gowenrw/cowboys_vs_dinosaurs/art/Card2-jack.png

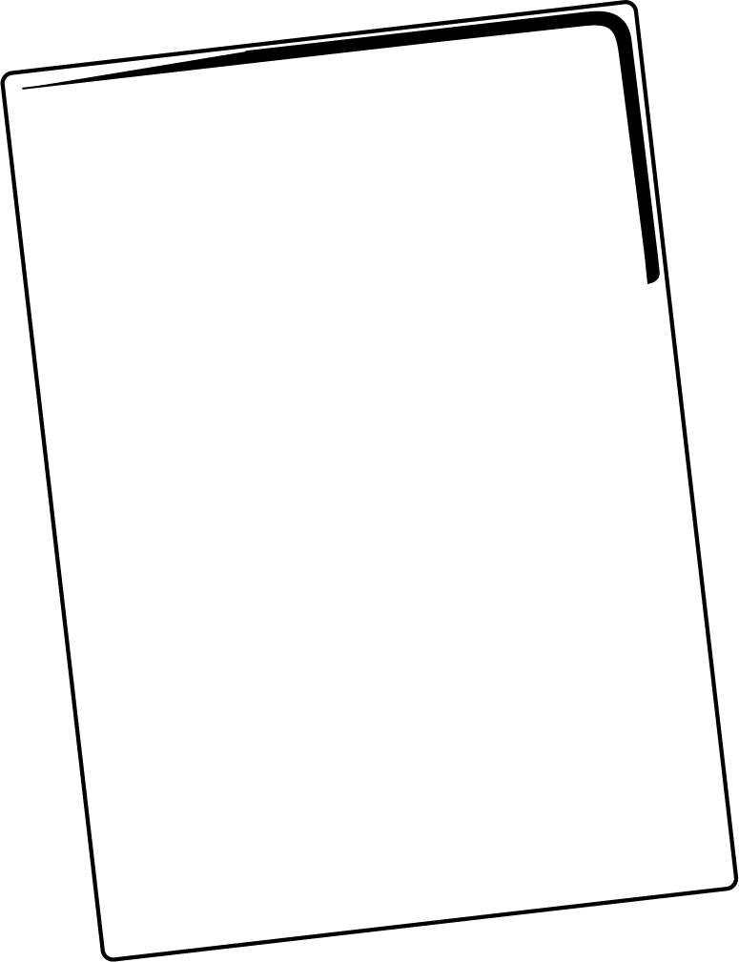
art/Card2-jack.png
