gowenrw/cowboys_vs_dinosaurs/art/Card2-king-01.png

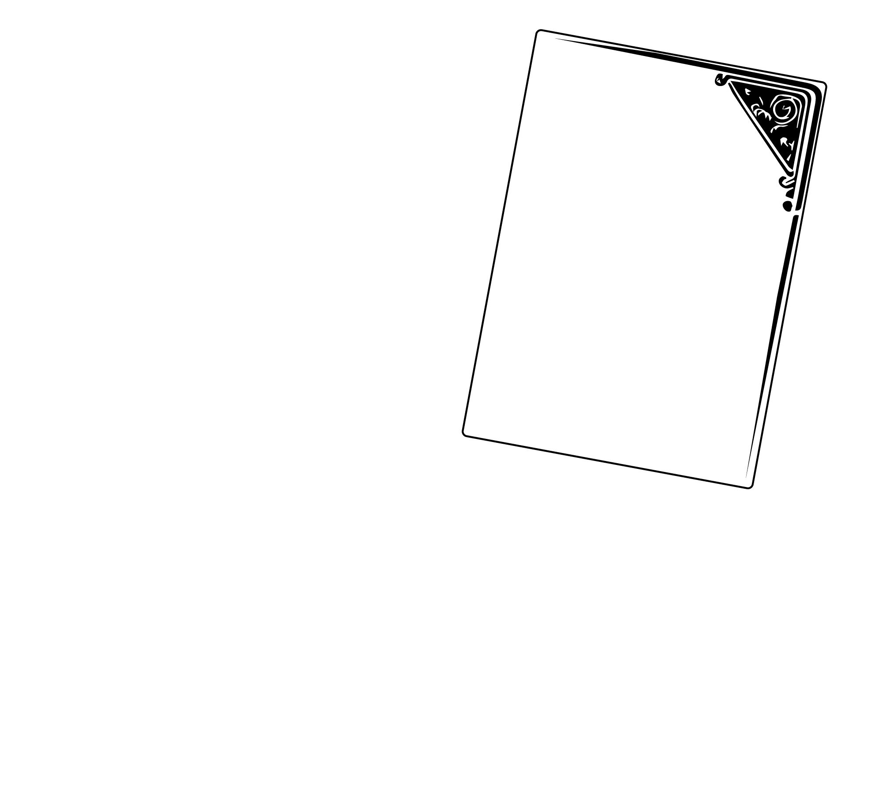
art/Card2-king-01.png
