gowenrw/cowboys_vs_dinosaurs/art/Card2-queen.png

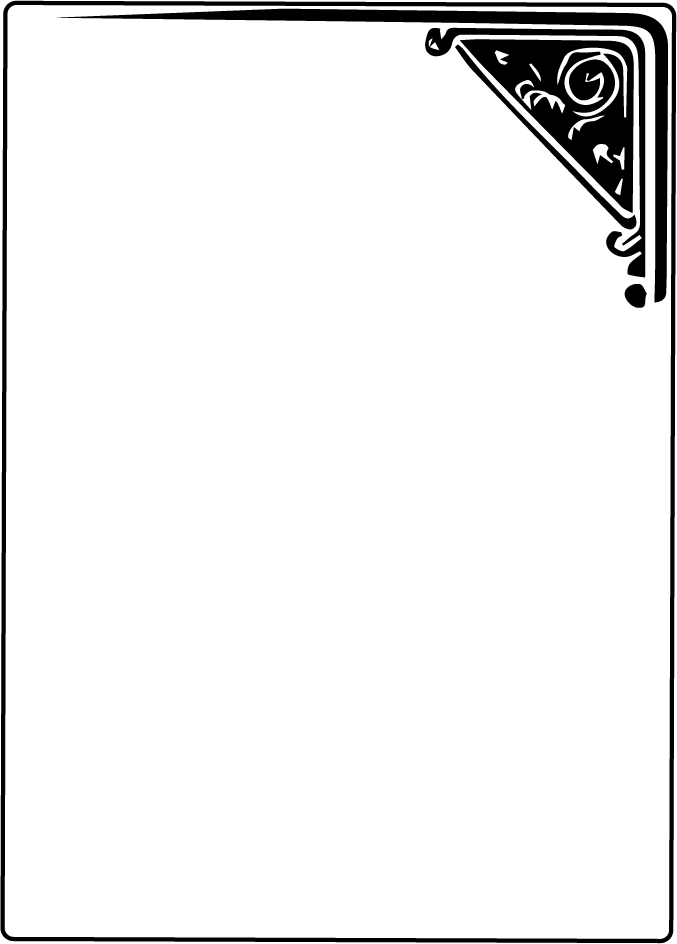
art/Card2-queen.png
