gowenrw/cowboys_vs_dinosaurs/art/Card2-suits-01.png

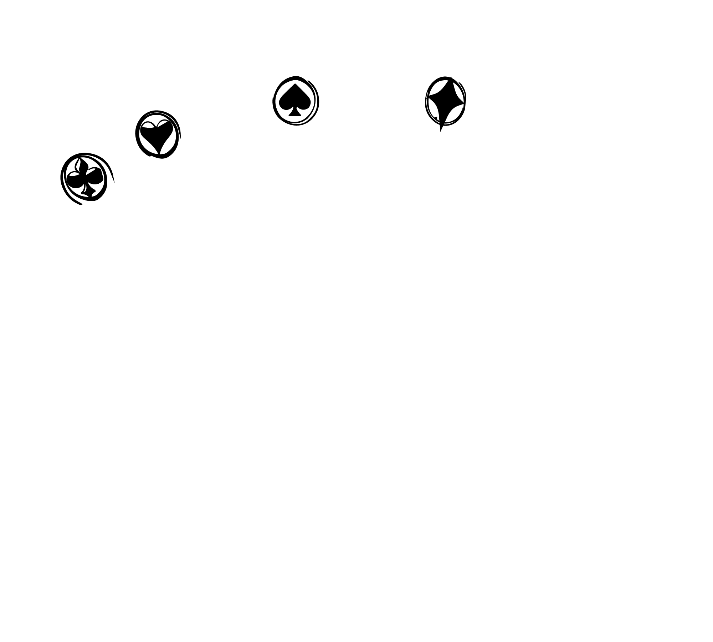
art/Card2-suits-01.png
