gowenrw/cowboys_vs_dinosaurs/art/Card2-ten.png

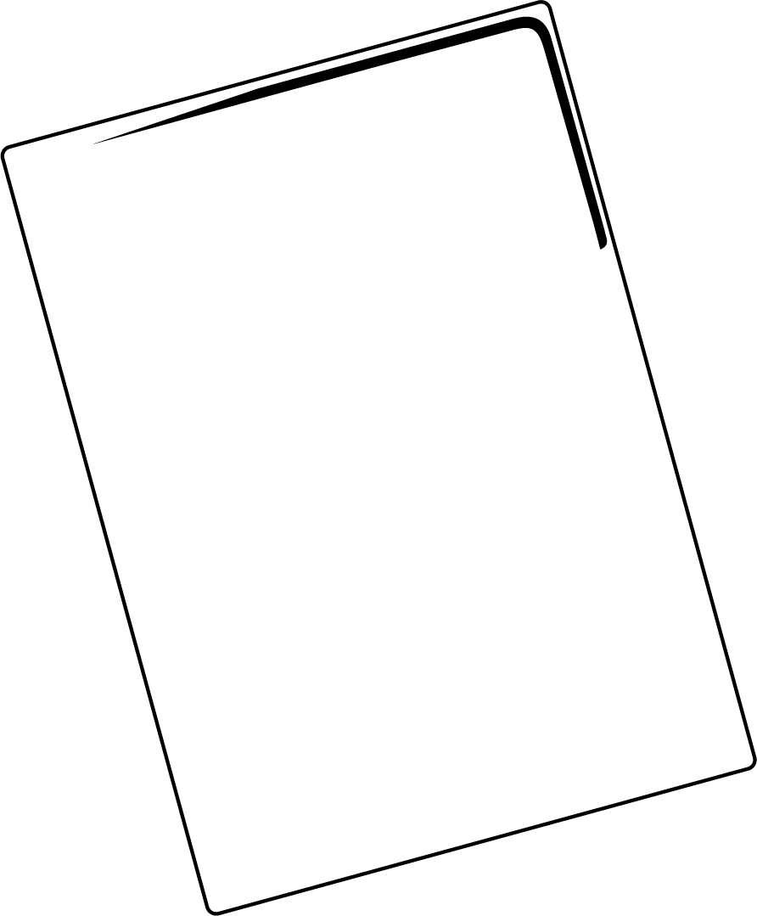
art/Card2-ten.png
