gowenrw/cowboys_vs_dinosaurs/art/card.png

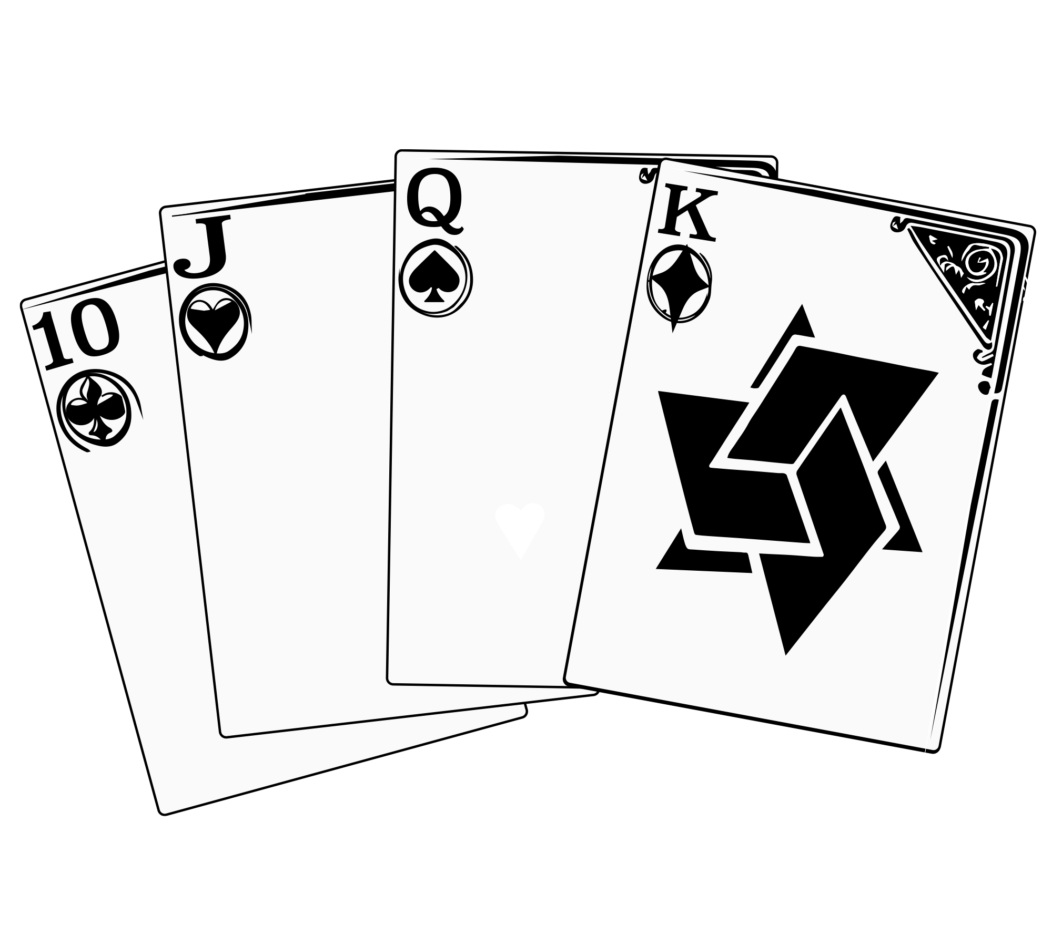
art/card.png
