gowenrw/cowboys_vs_dinosaurs/art/customlanyard_proof.png

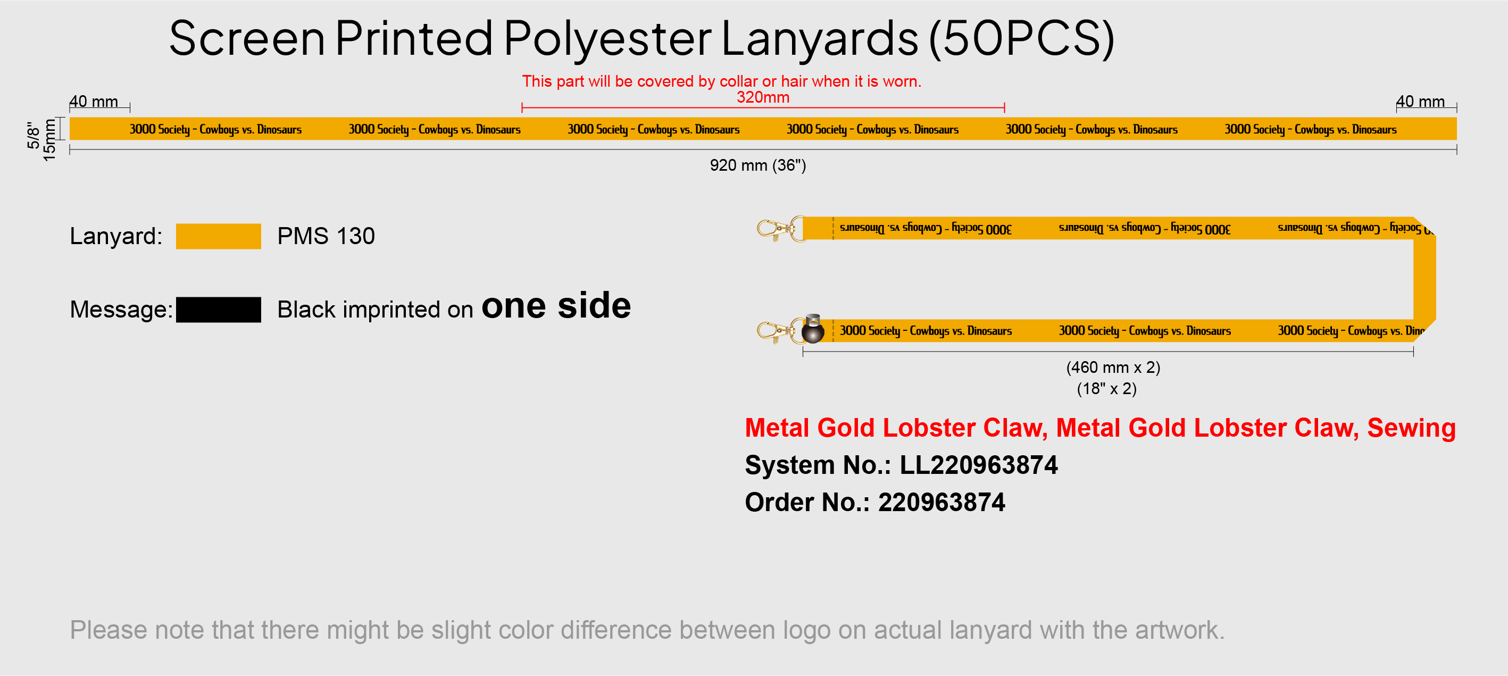
art/customlanyard_proof.png
