gowenrw/cowboys_vs_dinosaurs/art/CvD_Concept_Layout_2_Edge-01.jpg

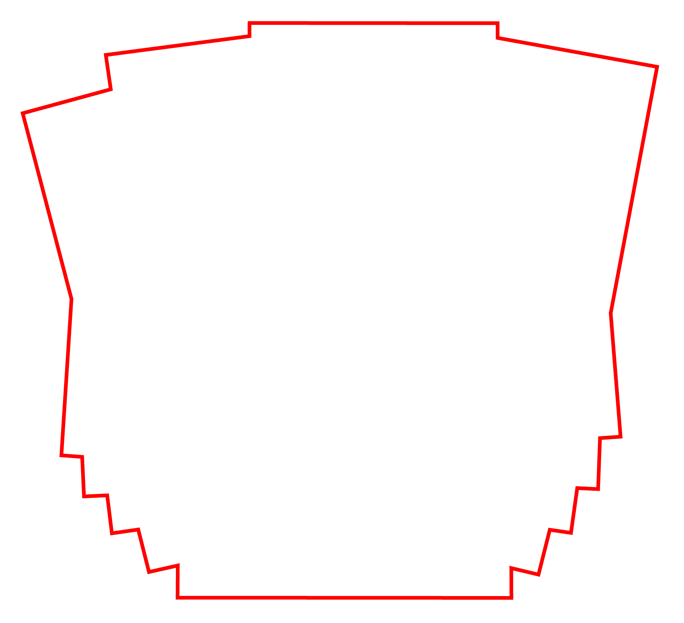
art/CvD_Concept_Layout_2_Edge-01.jpg
