gowenrw/cowboys_vs_dinosaurs/art/cvd_sticker.jpg

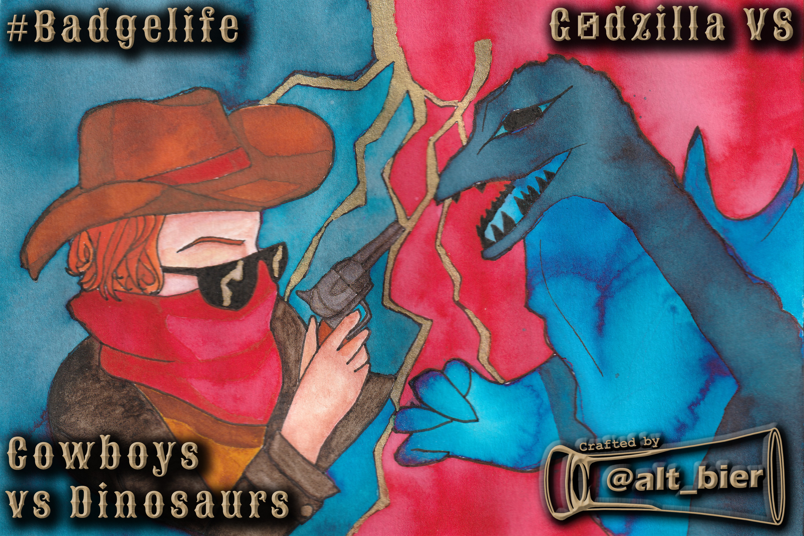
art/cvd_sticker.jpg
