gowenrw/cowboys_vs_dinosaurs/art/Dinosaurs_playing_poker_with_Cowboys_Rev01-01.png

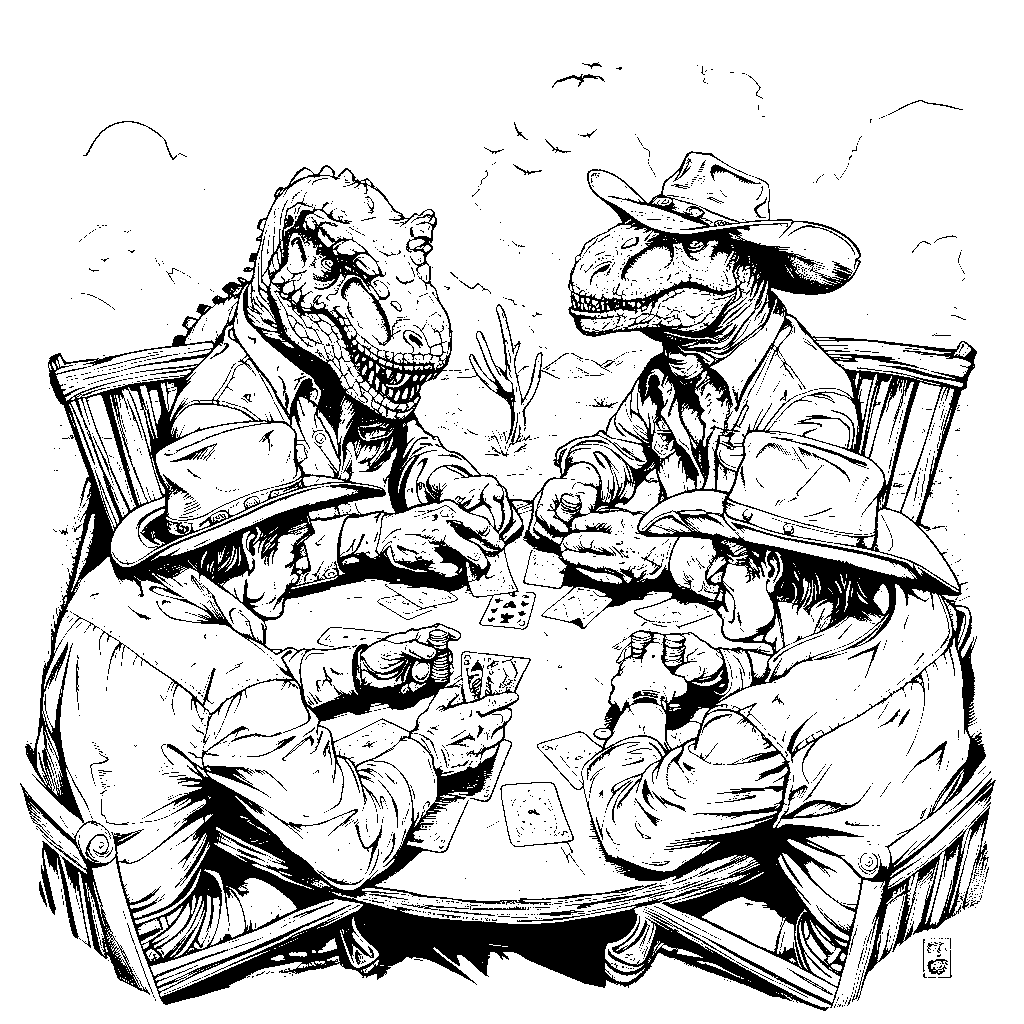
art/Dinosaurs_playing_poker_with_Cowboys_Rev01-01.png
