gowenrw/cowboys_vs_dinosaurs/art/Dinosaurs_playing_poker_with_Cowboys_Rev03_poker.png

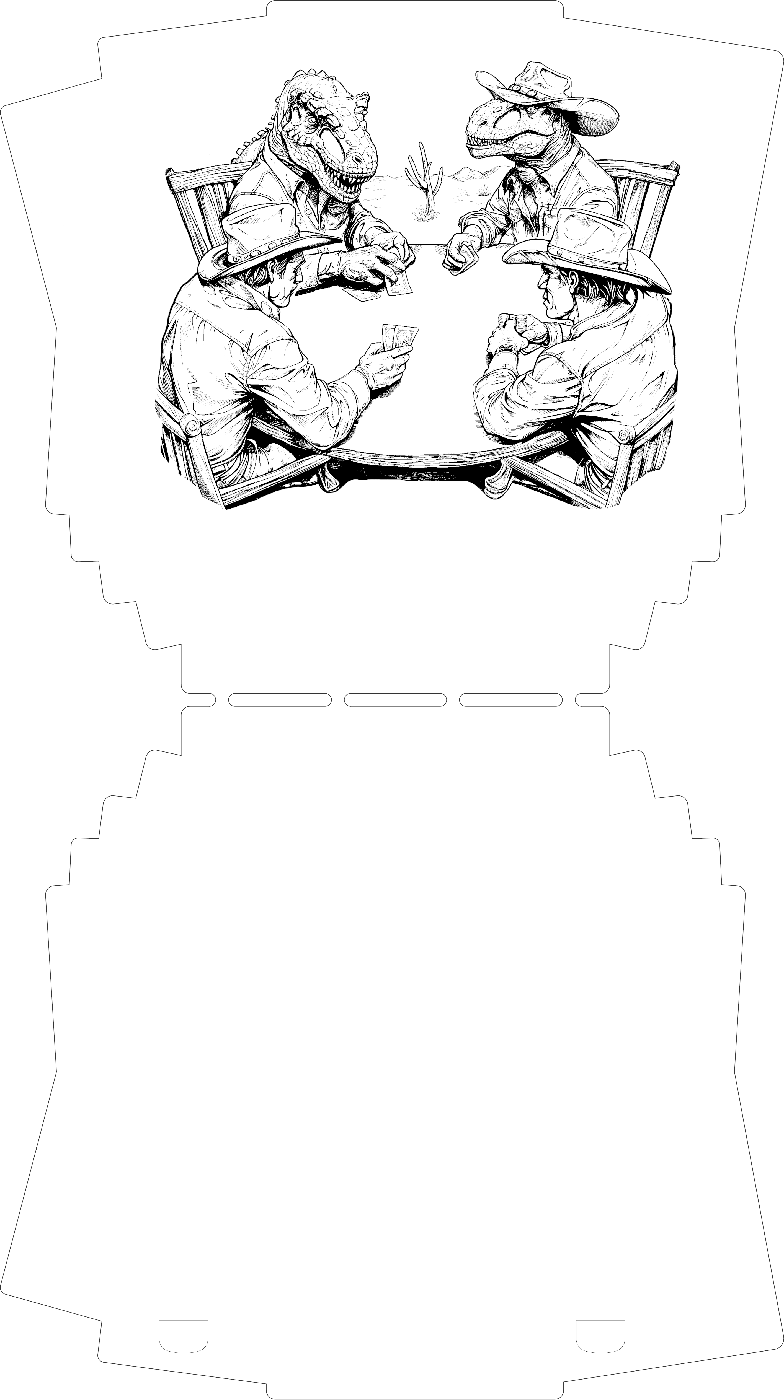
art/Dinosaurs_playing_poker_with_Cowboys_Rev03_poker.png
