gowenrw/cowboys_vs_dinosaurs/art/Dinosaurs_playing_poker_with_Cowboys_Rev03_tableback_mask.png

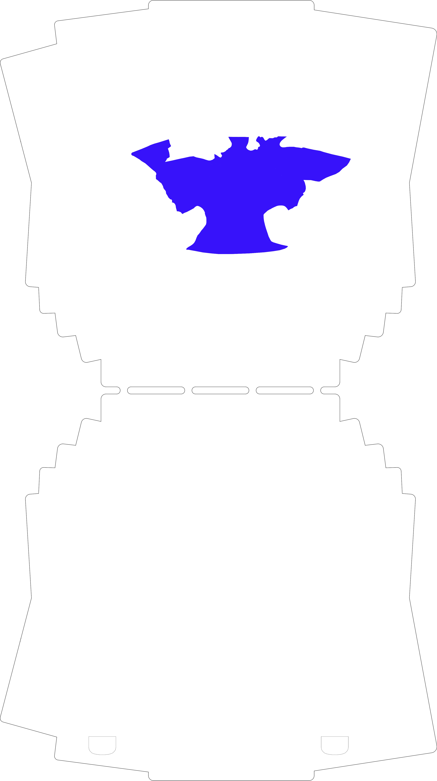
art/Dinosaurs_playing_poker_with_Cowboys_Rev03_tableback_mask.png
