gowenrw/cowboys_vs_dinosaurs/art/Dinosaurs_playing_poker_with_Cowboys_Rev04_cards_top.png

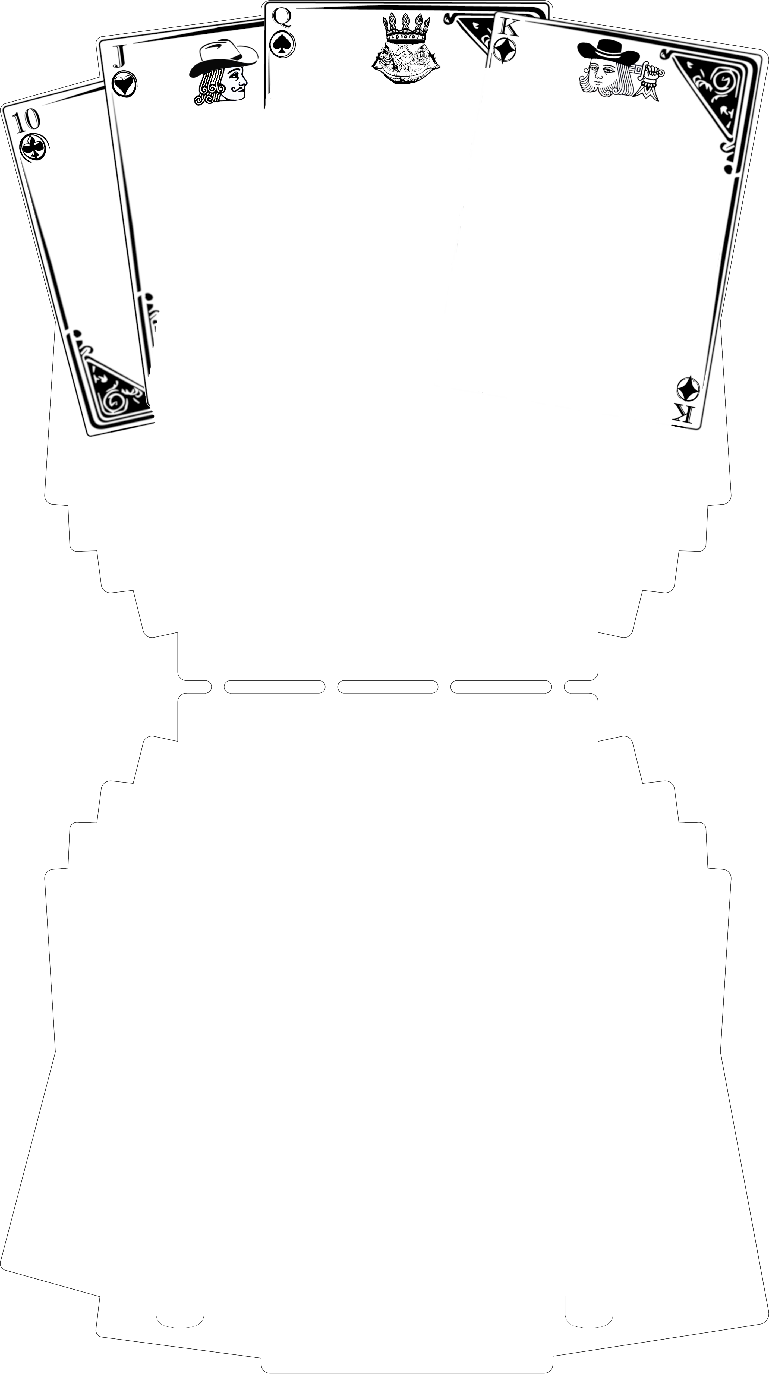
art/Dinosaurs_playing_poker_with_Cowboys_Rev04_cards_top.png
