gowenrw/cowboys_vs_dinosaurs/art/inspiration/alt_bier_cowbow_fighting_dinosaur_western_desert_f3125613-8451-445c-b527-2a0ff5816ff6.png

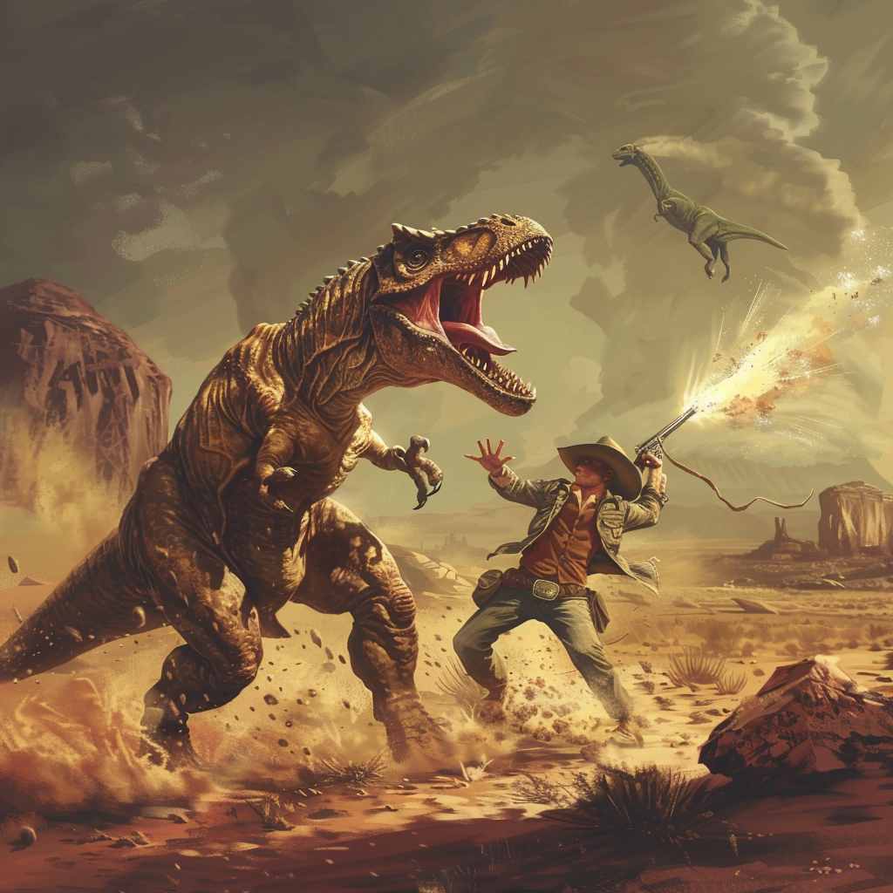
art/inspiration/alt_bier_cowbow_fighting_dinosaur_western_desert_f3125613-8451-445c-b527-2a0ff5816ff6.png
