gowenrw/cowboys_vs_dinosaurs/art/inspiration/alt_bier_cowbows_fighting_dinosaurs_on_western_plains_lineart_a25336c1-f8a5-47d8-abfa-79130a526ea2.png

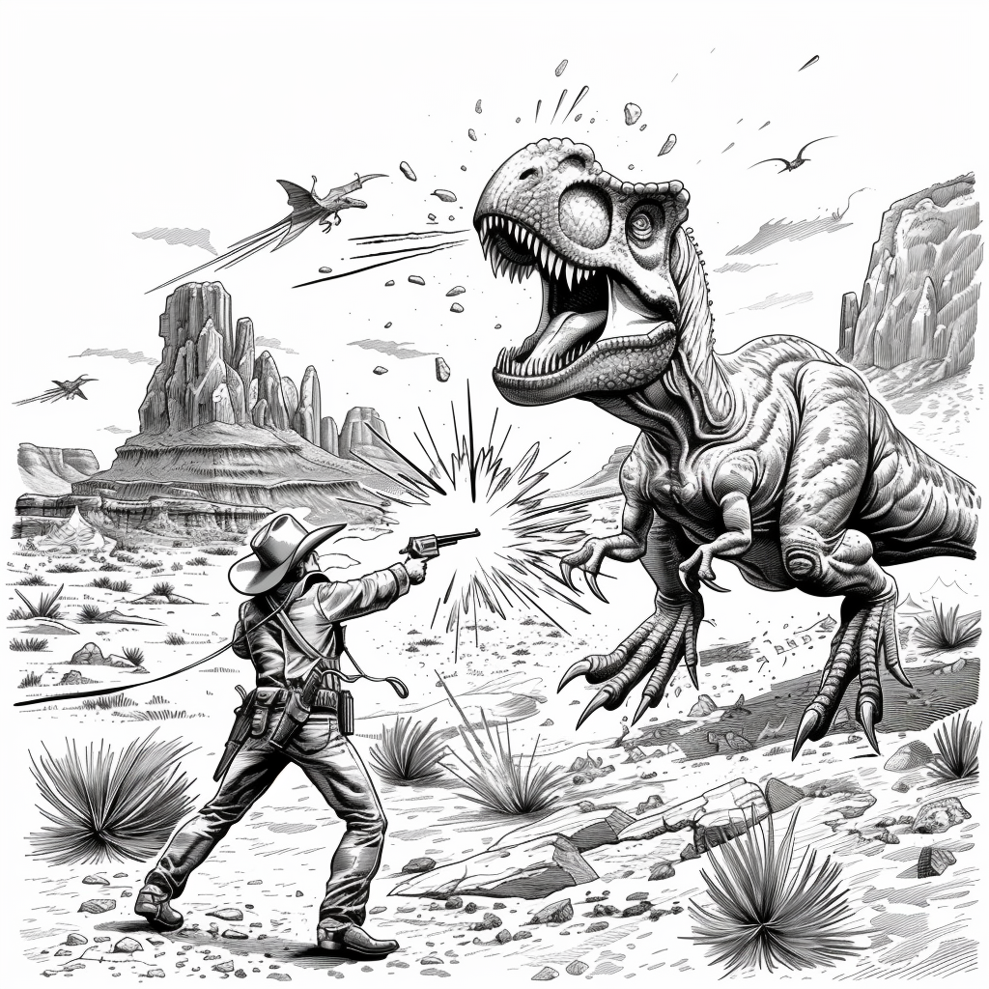
art/inspiration/alt_bier_cowbows_fighting_dinosaurs_on_western_plains_lineart_a25336c1-f8a5-47d8-abfa-79130a526ea2.png
