gowenrw/cowboys_vs_dinosaurs/art/inspiration/alt_bier_cowbows_fighting_dinosaurs_on_western_plains_lineart_f211f42e-96e7-4485-8ce5-57ef15629b50.png

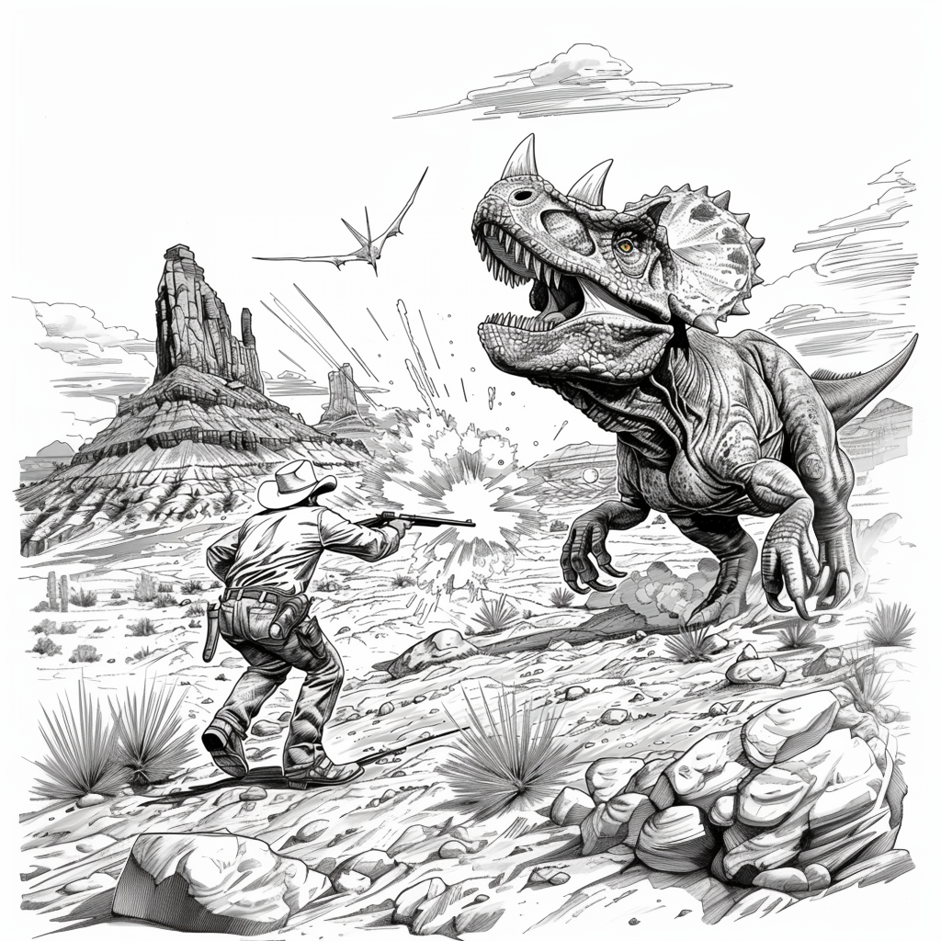
art/inspiration/alt_bier_cowbows_fighting_dinosaurs_on_western_plains_lineart_f211f42e-96e7-4485-8ce5-57ef15629b50.png
