gowenrw/cowboys_vs_dinosaurs/art/inspiration/alt_bier_Cowboy_fighting_dinosaur_western_desert_lineart_in_the_3fcf7f37-1b51-49f2-8be1-fd573b53e4d1.png

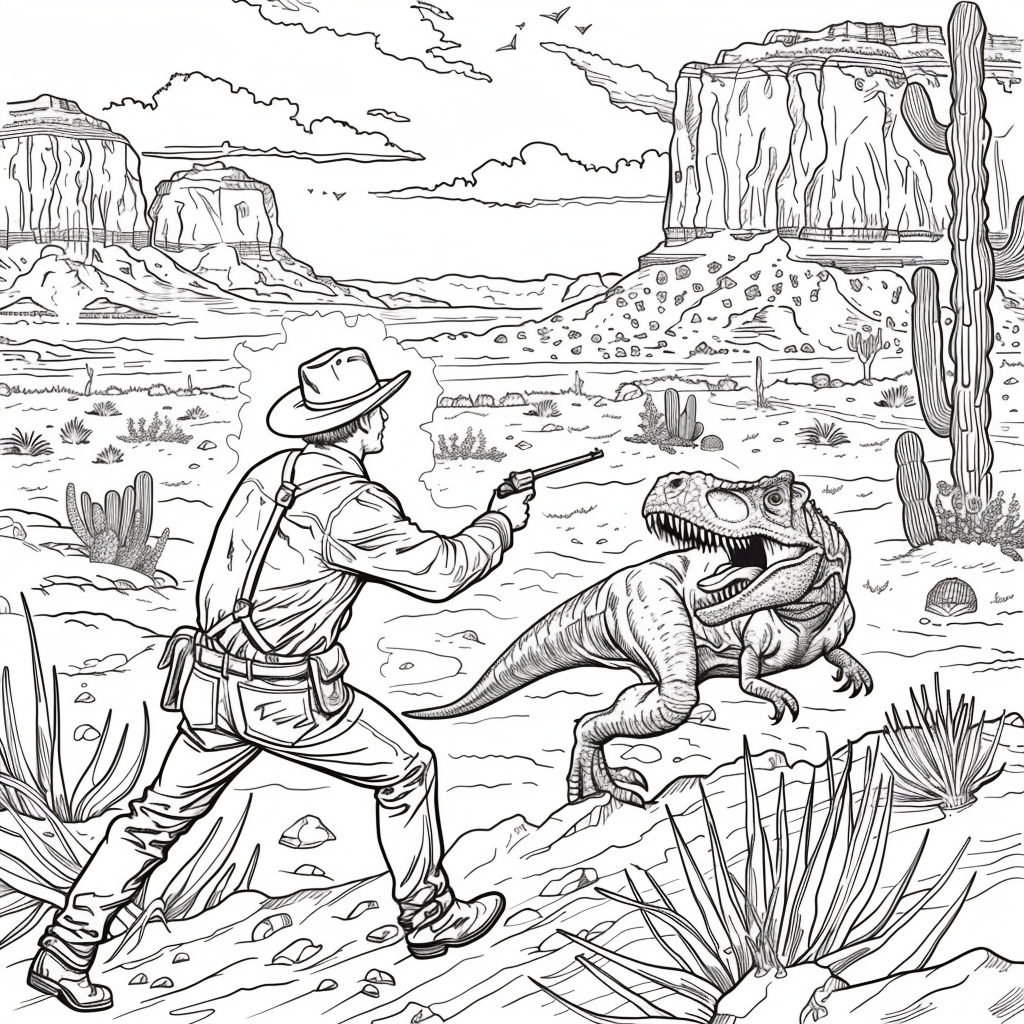
art/inspiration/alt_bier_Cowboy_fighting_dinosaur_western_desert_lineart_in_the_3fcf7f37-1b51-49f2-8be1-fd573b53e4d1.png
