gowenrw/cowboys_vs_dinosaurs/art/inspiration/alt_bier_Cowboy_fighting_dinosaur_western_desert_lineart_in_the_5abc0463-220d-4dce-b457-b19400f9878a.png

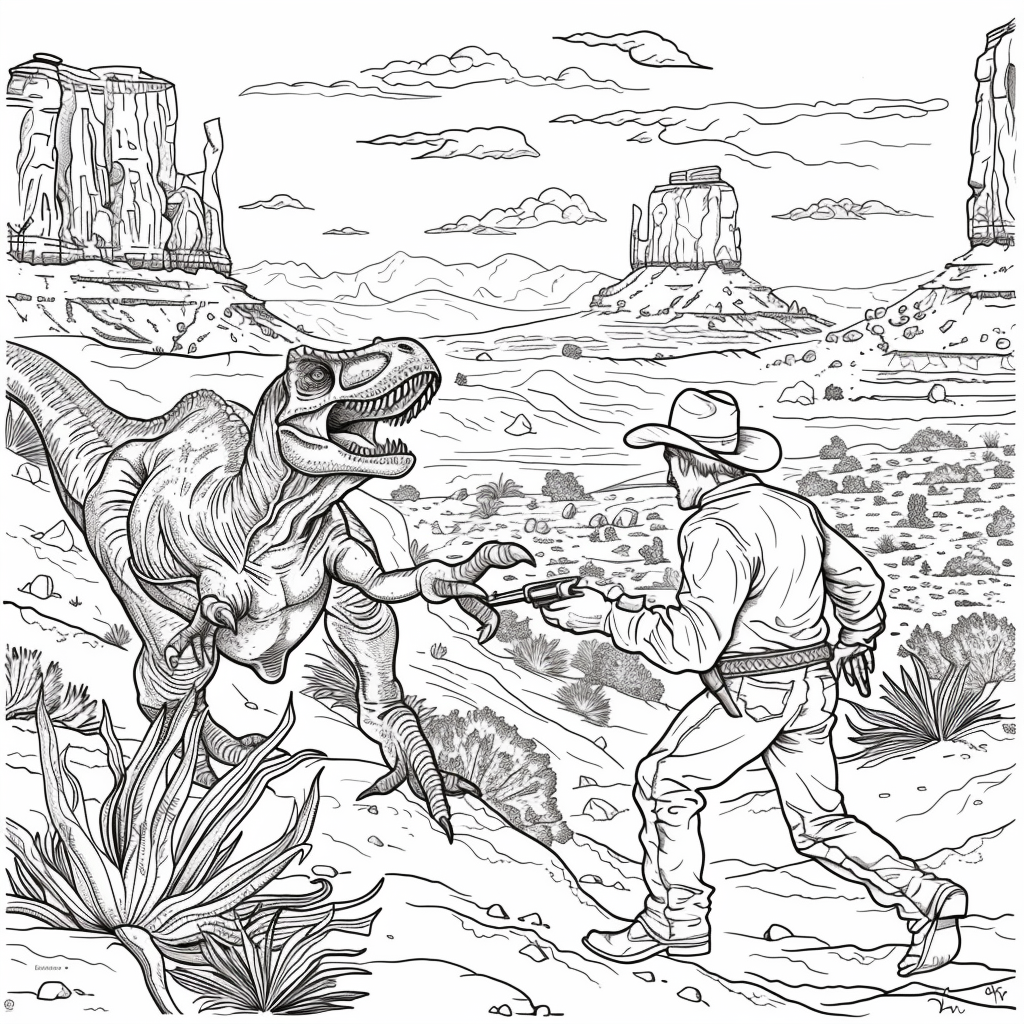
art/inspiration/alt_bier_Cowboy_fighting_dinosaur_western_desert_lineart_in_the_5abc0463-220d-4dce-b457-b19400f9878a.png
