gowenrw/cowboys_vs_dinosaurs/art/inspiration/alt_bier_Cowboy_fighting_dinosaur_western_desert_lineart_in_the_125ab11b-fa4d-480e-95ab-365c5027ad4b.png

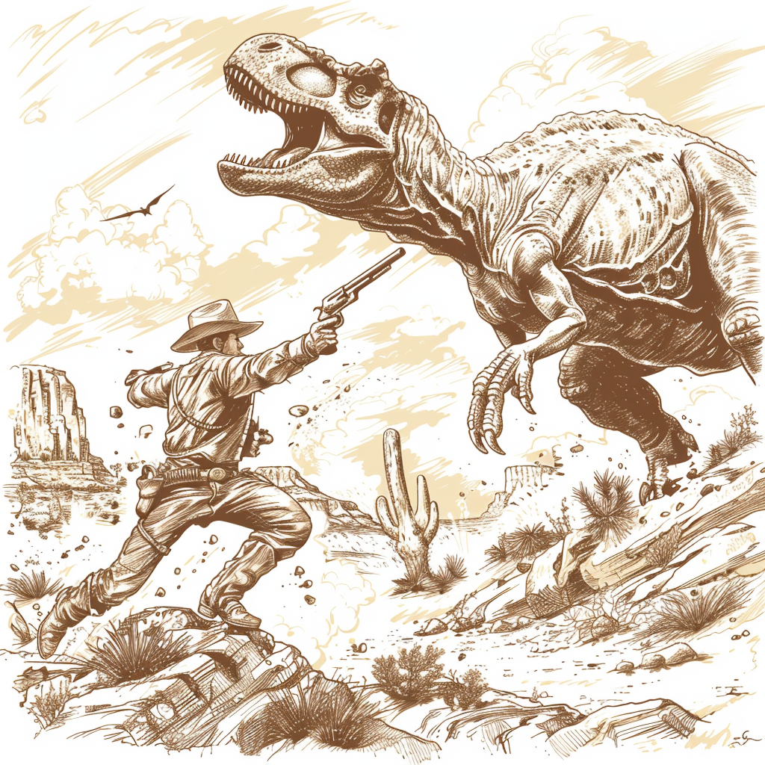
art/inspiration/alt_bier_Cowboy_fighting_dinosaur_western_desert_lineart_in_the_125ab11b-fa4d-480e-95ab-365c5027ad4b.png
