gowenrw/cowboys_vs_dinosaurs/art/inspiration/alt_bier_Cowboy_fighting_dinosaur_western_desert_lineart_in_the_282fbab5-89a2-4fbe-8cb0-ce9cdb12c011.png

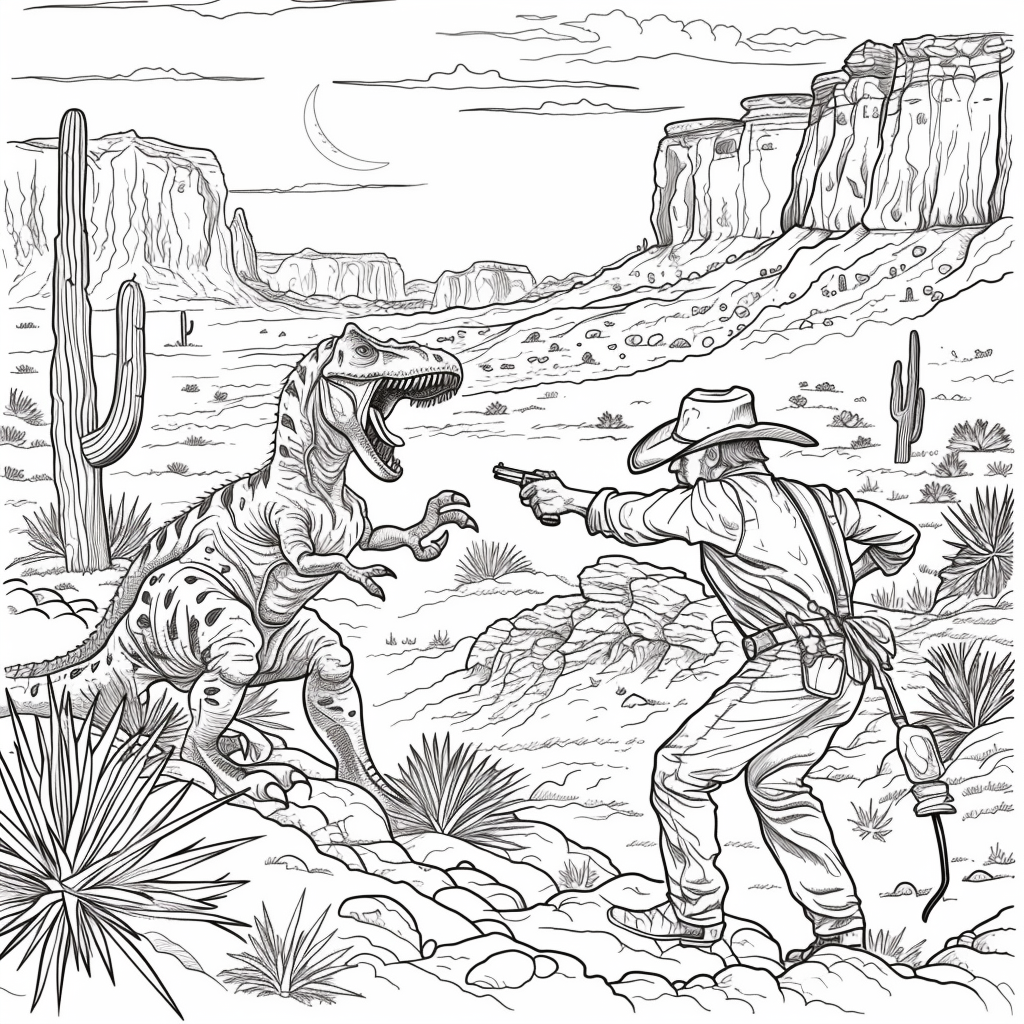
art/inspiration/alt_bier_Cowboy_fighting_dinosaur_western_desert_lineart_in_the_282fbab5-89a2-4fbe-8cb0-ce9cdb12c011.png
