gowenrw/cowboys_vs_dinosaurs/art/inspiration/alt_bier_Cowboy_fighting_dinosaur_western_desert_lineart_in_the_556321d8-3b47-4c62-af58-bf69dc58ff7b.png

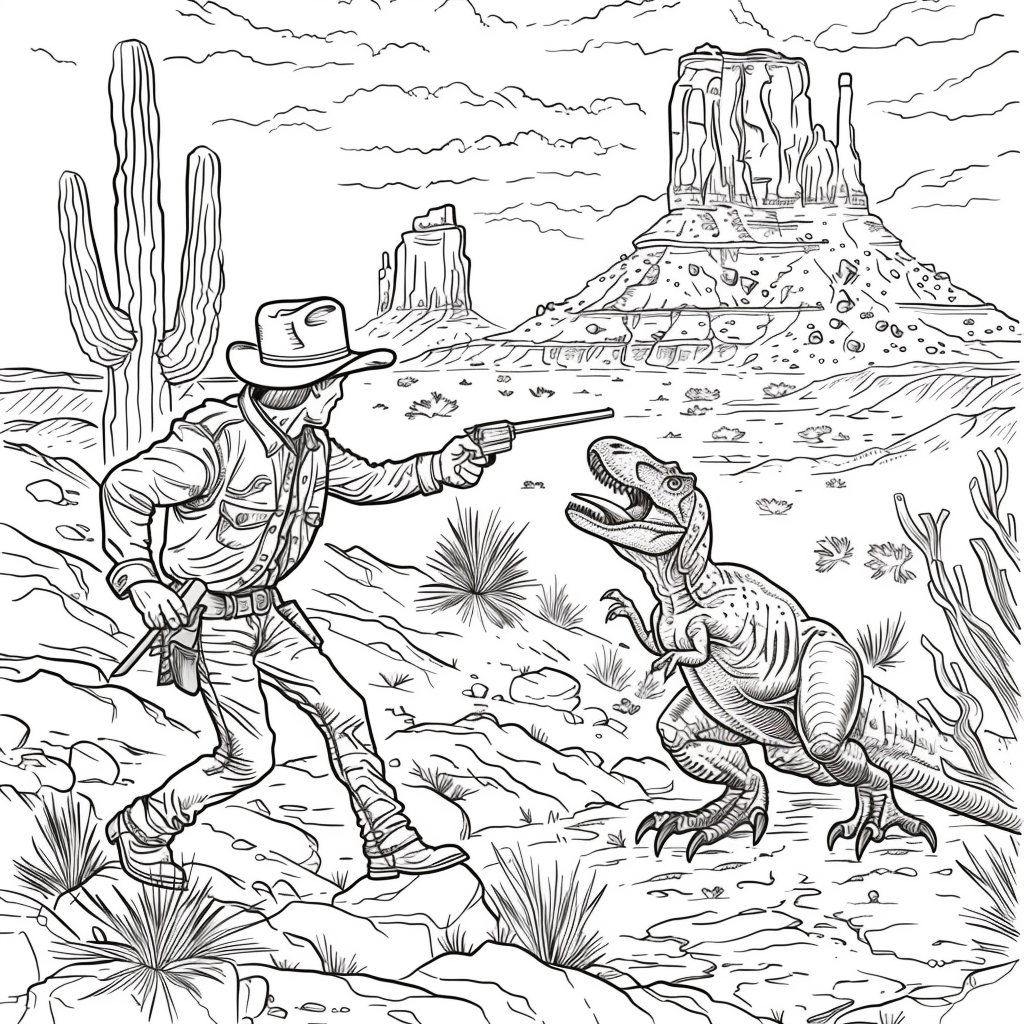
art/inspiration/alt_bier_Cowboy_fighting_dinosaur_western_desert_lineart_in_the_556321d8-3b47-4c62-af58-bf69dc58ff7b.png
