gowenrw/cowboys_vs_dinosaurs/art/inspiration/alt_bier_Cowboy_shooting_at_a_giant_Tyrannosaurus_western_deser_4aaeae45-6dd6-4bee-8e14-5fdc8e3b1cd2.png

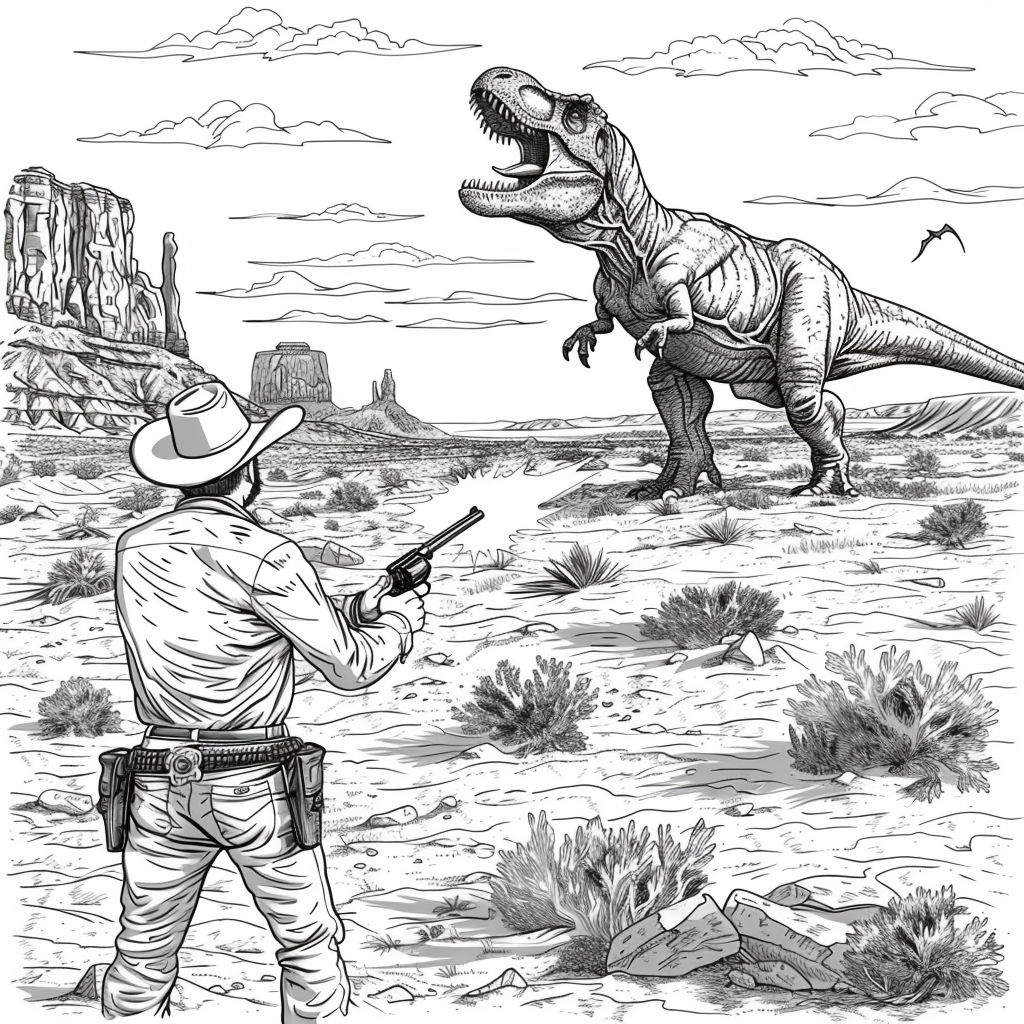
art/inspiration/alt_bier_Cowboy_shooting_at_a_giant_Tyrannosaurus_western_deser_4aaeae45-6dd6-4bee-8e14-5fdc8e3b1cd2.png
