gowenrw/cowboys_vs_dinosaurs/art/inspiration/alt_bier_Cowboy_shooting_at_a_giant_Tyrannosaurus_western_deser_bf7210f8-492b-4deb-bcf0-d93d4ab07705.png

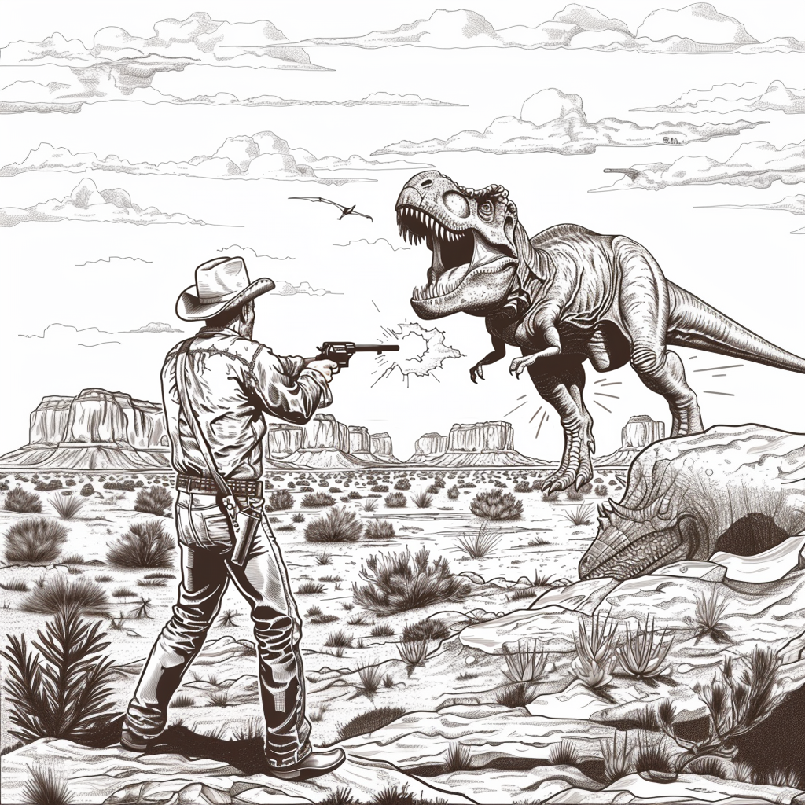
art/inspiration/alt_bier_Cowboy_shooting_at_a_giant_Tyrannosaurus_western_deser_bf7210f8-492b-4deb-bcf0-d93d4ab07705.png
