gowenrw/cowboys_vs_dinosaurs/art/inspiration/alt_bier_Dinosaurs_and_cowboys_playing_poker_coloring_book_no_c_4e8ae06e-67b5-412c-8ffb-398090f191ba.png

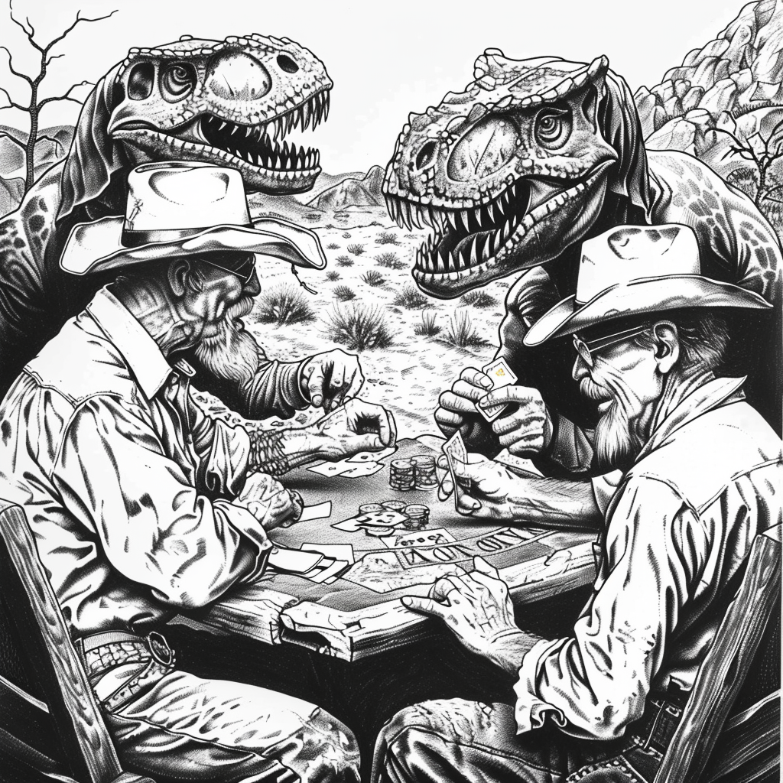
art/inspiration/alt_bier_Dinosaurs_and_cowboys_playing_poker_coloring_book_no_c_4e8ae06e-67b5-412c-8ffb-398090f191ba.png
