gowenrw/cowboys_vs_dinosaurs/art/inspiration/alt_bier_Dinosaurs_and_cowboys_playing_poker_in_the_style_of_do_59055e36-9cf2-4947-9dd1-eef9e1b4fb1d.png

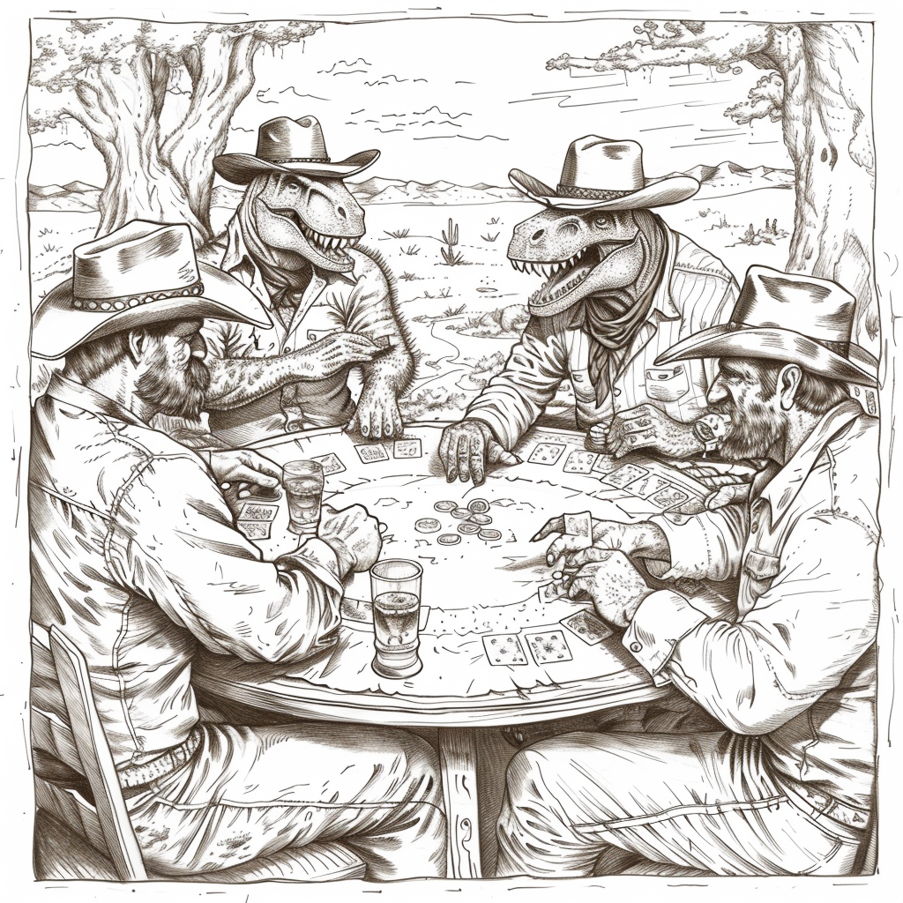
art/inspiration/alt_bier_Dinosaurs_and_cowboys_playing_poker_in_the_style_of_do_59055e36-9cf2-4947-9dd1-eef9e1b4fb1d.png
