gowenrw/cowboys_vs_dinosaurs/art/inspiration/alt_bier_Dinosaurs_playing_poker_with_cowboys_in_the_style_of_D_9a29f2ae-062c-44e6-b967-7e2f51b78c59.png

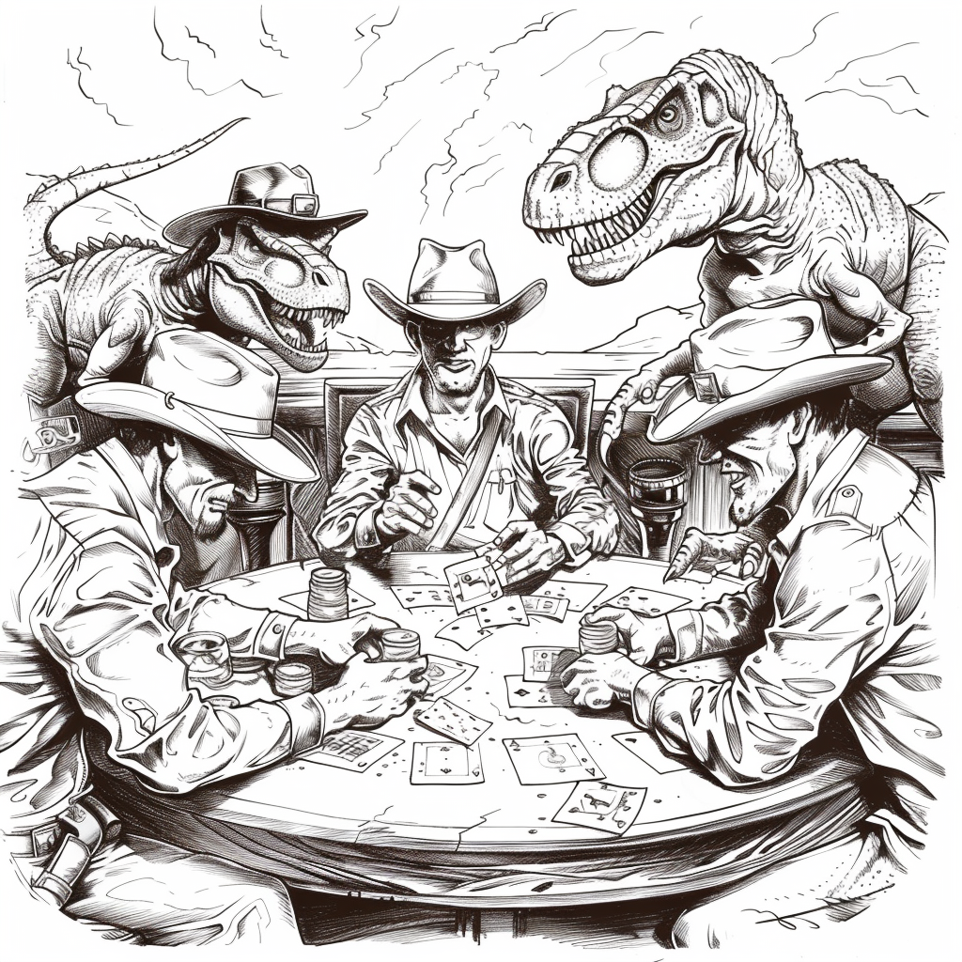
art/inspiration/alt_bier_Dinosaurs_playing_poker_with_cowboys_in_the_style_of_D_9a29f2ae-062c-44e6-b967-7e2f51b78c59.png
