gowenrw/cowboys_vs_dinosaurs/art/inspiration/alt_bier_Dinosaurs_playing_poker_with_cowboys_in_the_style_of_D_9ae7338b-8200-457a-bcaf-93dff62f932e.png

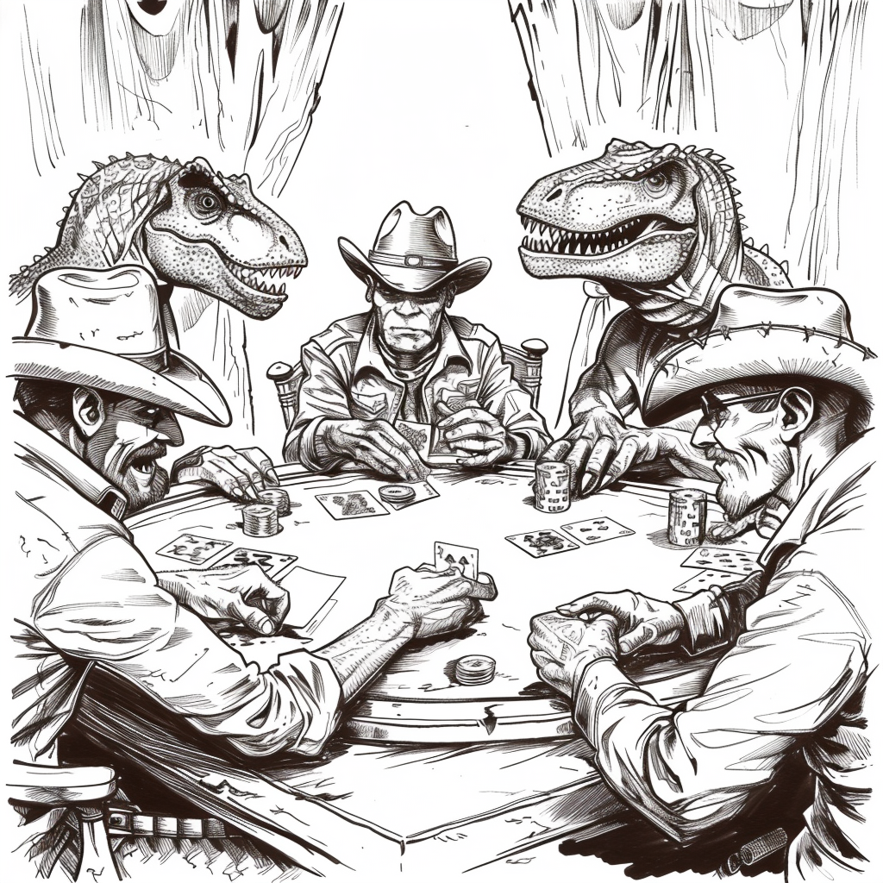
art/inspiration/alt_bier_Dinosaurs_playing_poker_with_cowboys_in_the_style_of_D_9ae7338b-8200-457a-bcaf-93dff62f932e.png
