gowenrw/cowboys_vs_dinosaurs/art/labels/cowboys_vs_dinos_ass.jpg

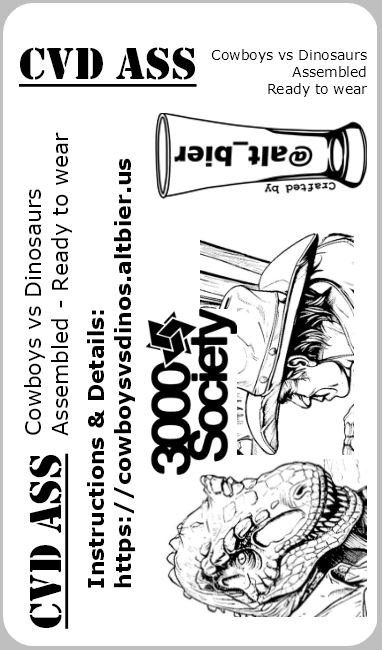
art/labels/cowboys_vs_dinos_ass.jpg
