gowenrw/cowboys_vs_dinosaurs/art/Lanyard_txt.png

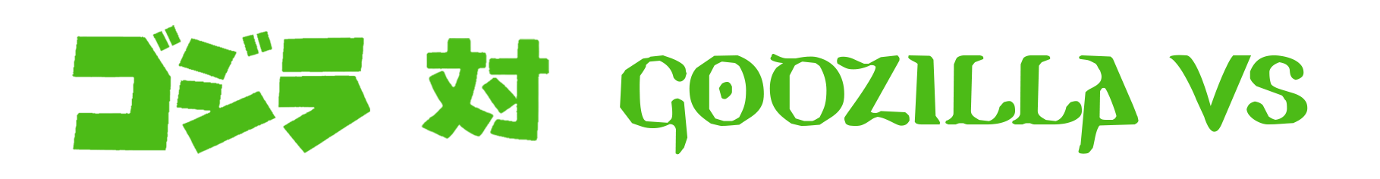
art/Lanyard_txt.png
