gowenrw/cowboys_vs_dinosaurs/art/merged.png

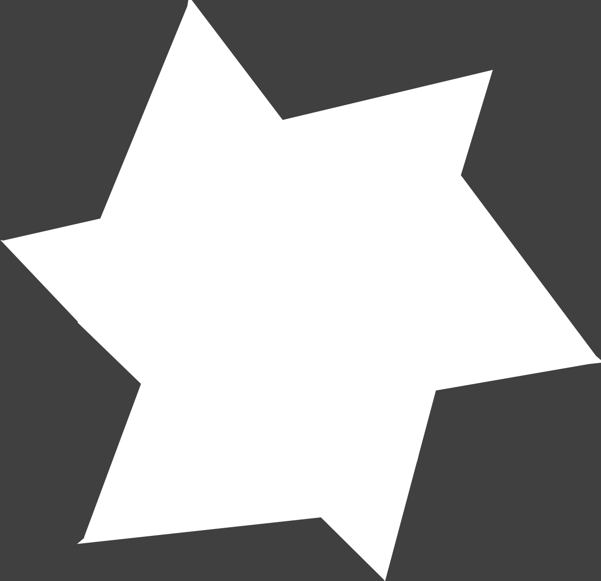
art/merged.png
