gowenrw/cowboys_vs_dinosaurs/docs/20240402_095641.jpg

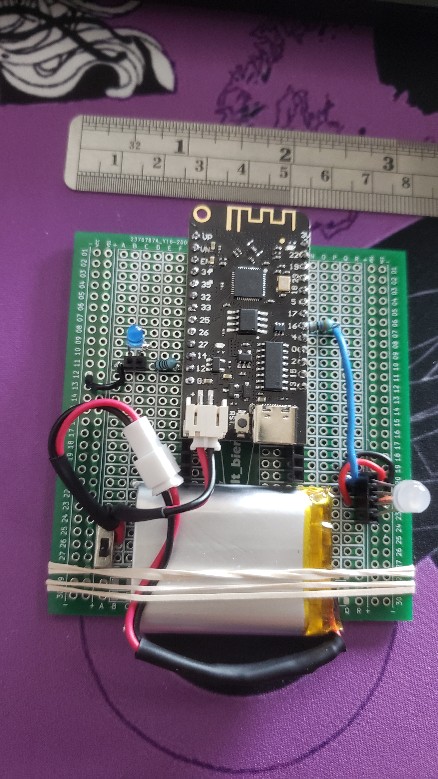
docs/20240402_095641.jpg
