gowenrw/cowboys_vs_dinosaurs/docs/20240514_150416.jpg

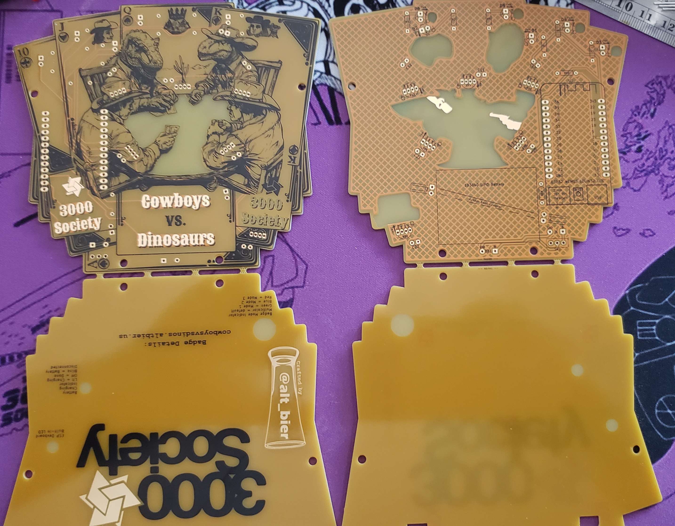
docs/20240514_150416.jpg
