gowenrw/cowboys_vs_dinosaurs/docs/20240630_174120.jpg

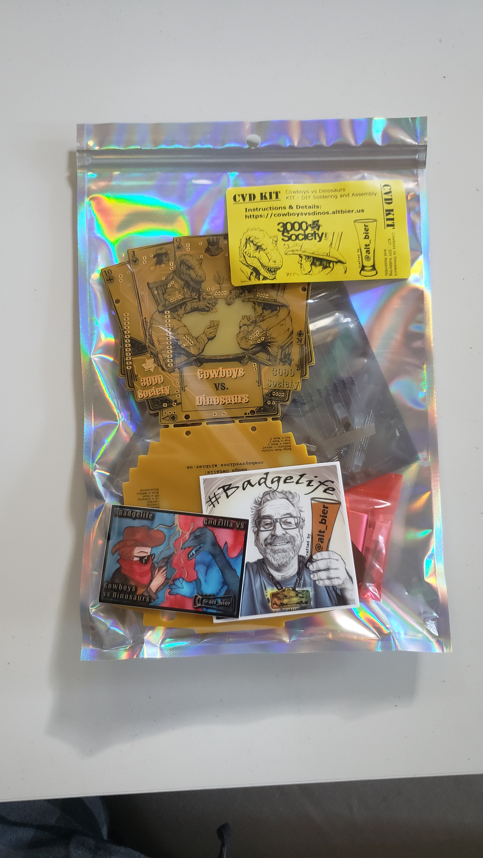
docs/20240630_174120.jpg
