gowenrw/cowboys_vs_dinosaurs/docs/20240630_174721.jpg

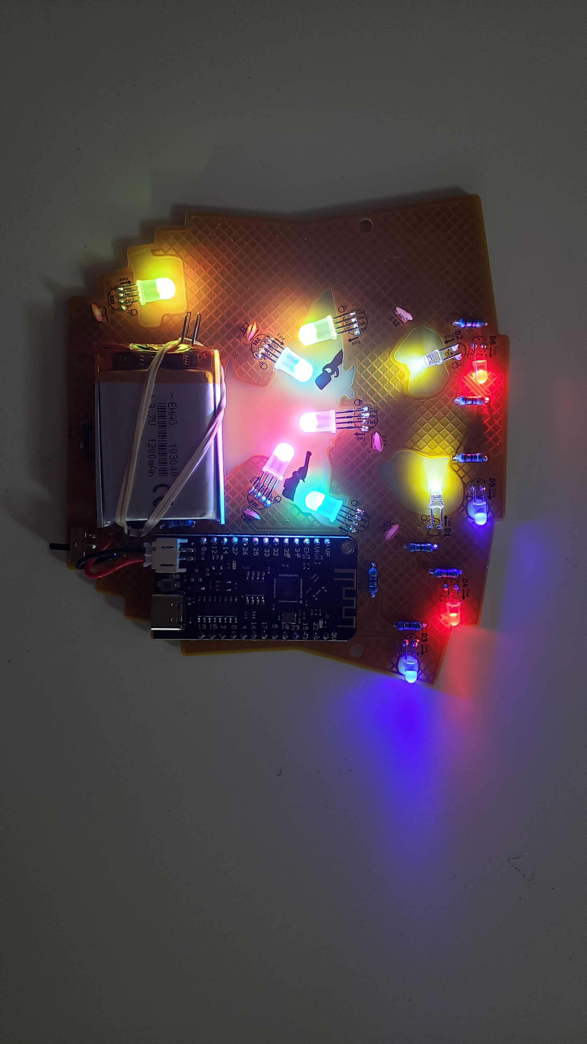
docs/20240630_174721.jpg
