gowenrw/cowboys_vs_dinosaurs/docs/cvd_schematic.jpg

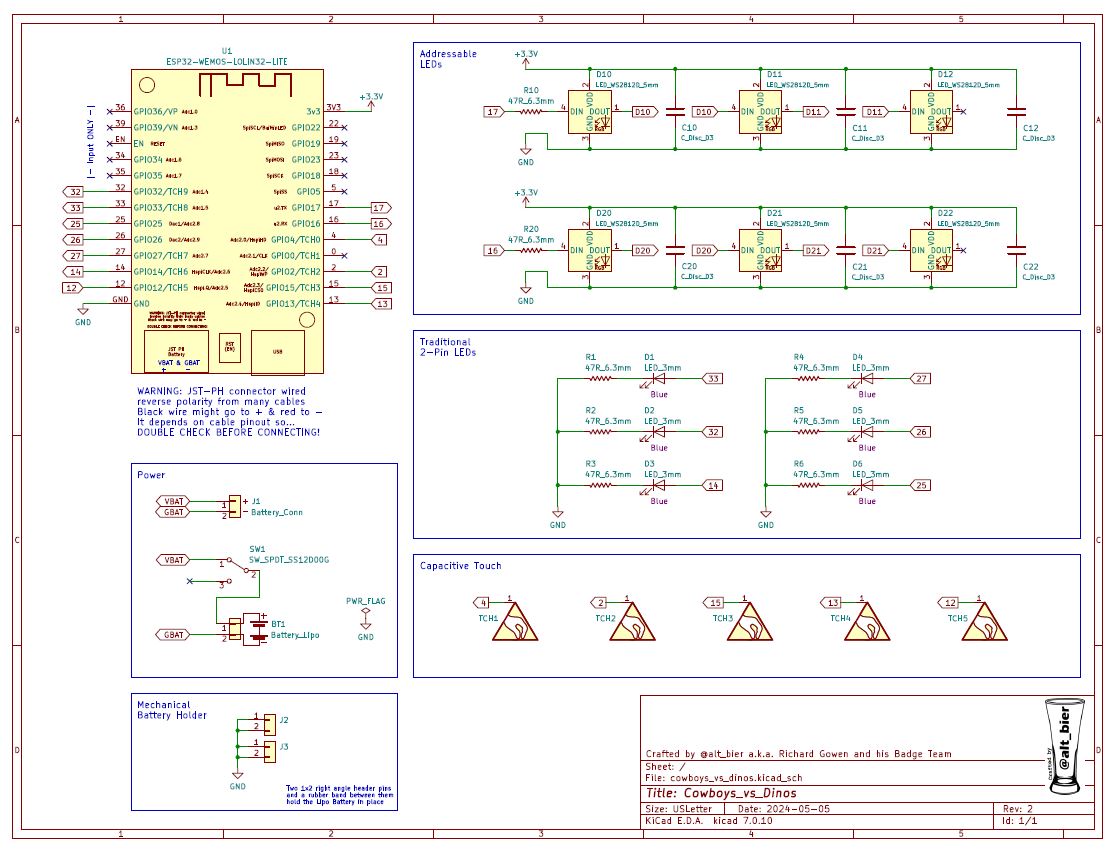
docs/cvd_schematic.jpg
