gowenrw/cowboys_vs_dinosaurs/eda/cowboys_vs_dinos/gerber/PCBWAY-DrillSettings.JPG

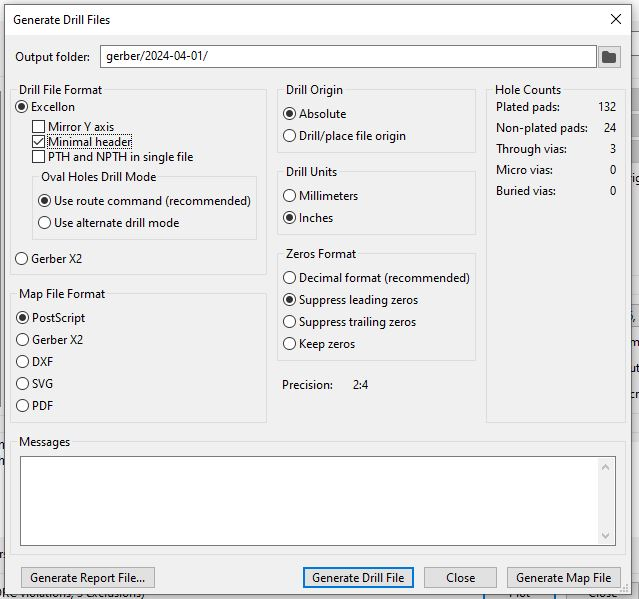
eda/cowboys_vs_dinos/gerber/PCBWAY-DrillSettings.JPG
