gowenrw/cowboys_vs_dinosaurs/eda/cowboys_vs_dinos/gerber/PCBWAY-GerberSetting.JPG

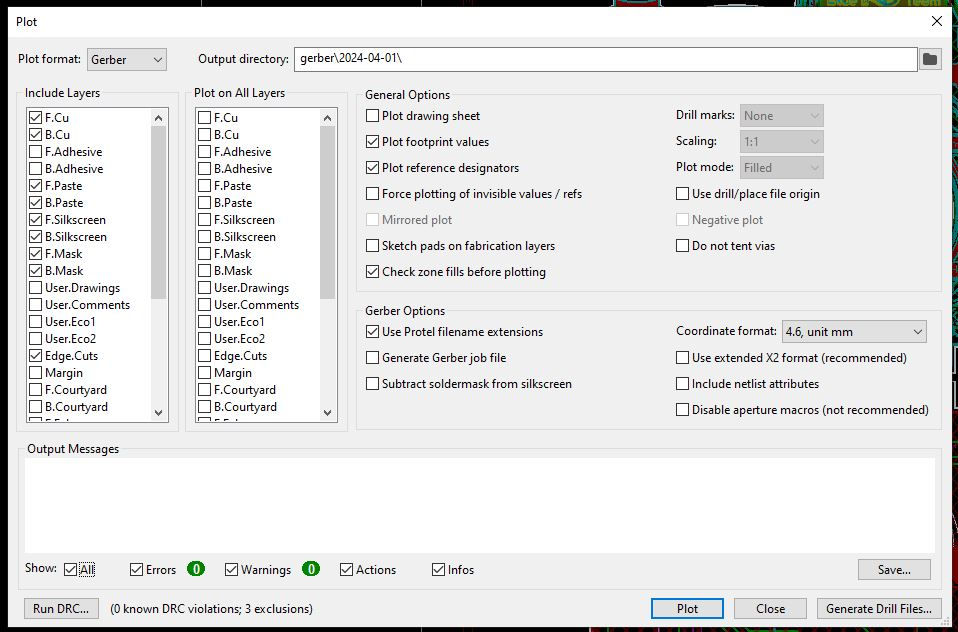
eda/cowboys_vs_dinos/gerber/PCBWAY-GerberSetting.JPG
