gowenrw/cowboys_vs_dinosaurs/eda/cowboys_vs_dinos/snapshots/cowboys_vs_dinos_3d_draft03.png

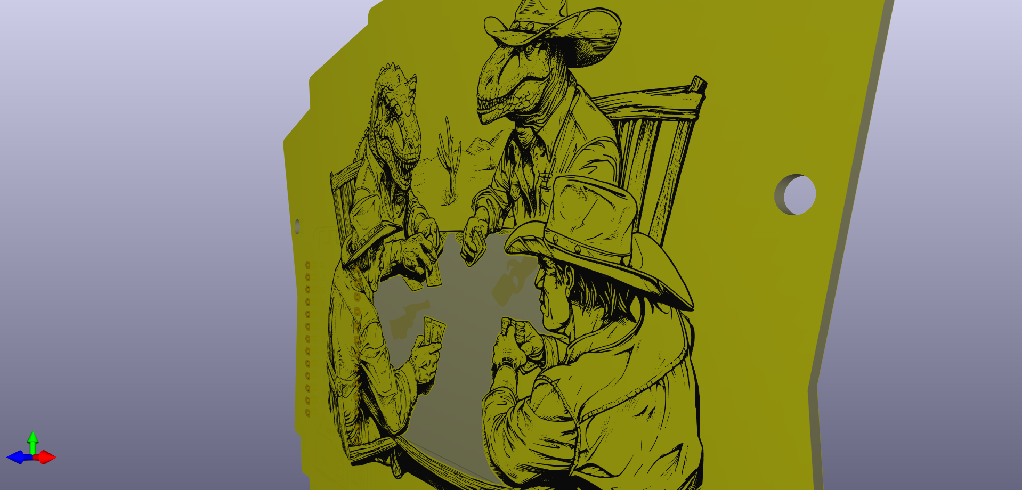
eda/cowboys_vs_dinos/snapshots/cowboys_vs_dinos_3d_draft03.png
