gowenrw/cowboys_vs_dinosaurs/eda/cowboys_vs_dinos/3d_models/Battery_Holder_CR2032_BS-2-1.stp

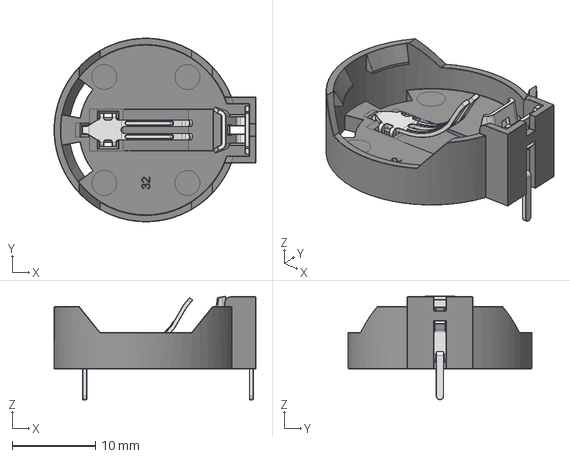
[picture p93: CAD file, 2024-03-11]
eda/cowboys_vs_dinos/3d_models/Battery_Holder_CR2032_BS-2-1.stp
24.3 x 22.1 x 12.5 mm
