gowenrw/cowboys_vs_dinosaurs/eda/cowboys_vs_dinos/3d_models/LED_0805_2012Metric_Castellated.step

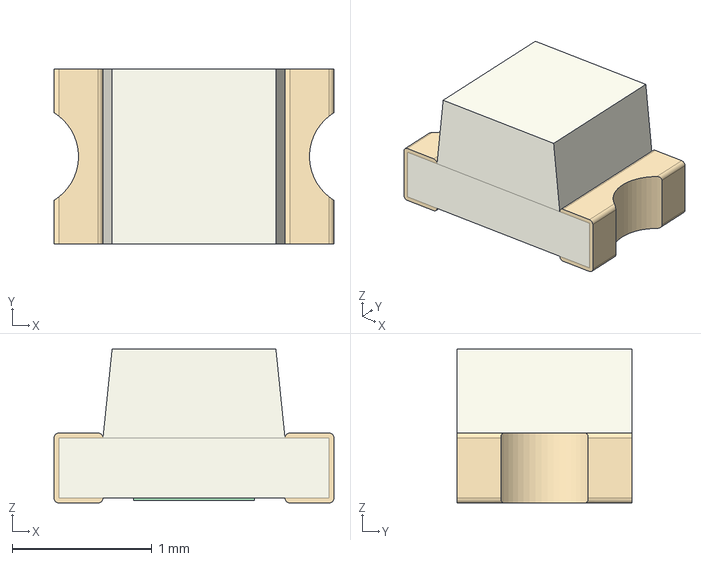
[picture p95: CAD file, 2024-03-11]
eda/cowboys_vs_dinos/3d_models/LED_0805_2012Metric_Castellated.step
2.00 x 1.25 x 1.10 mm
