gowenrw/cowboys_vs_dinosaurs/eda/cowboys_vs_dinos/3d_models/PinHeader_1x15_P2.54mm_Horizontal.step

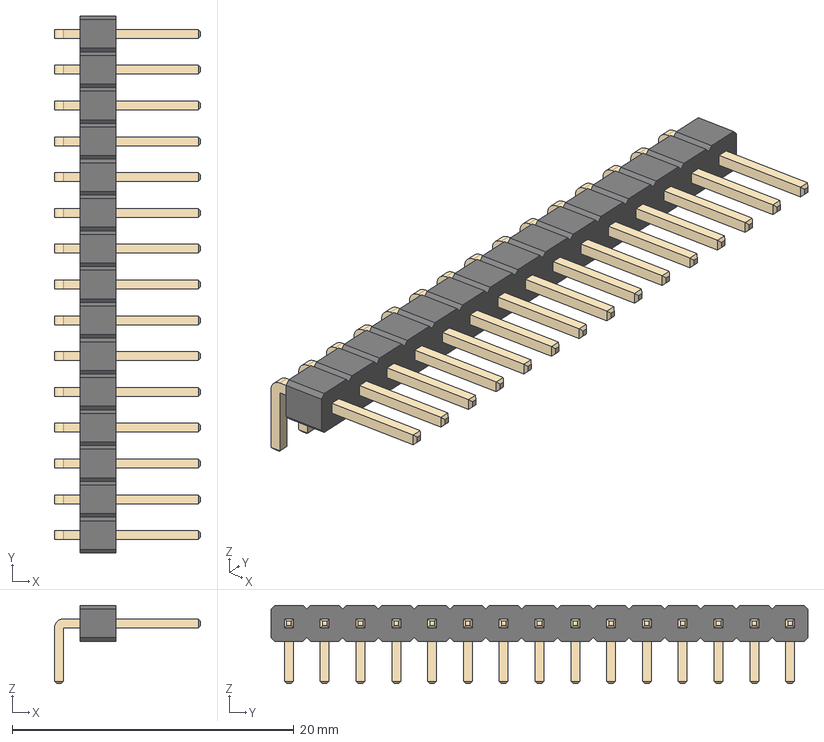
[picture p97: CAD file, 2024-03-11]
eda/cowboys_vs_dinos/3d_models/PinHeader_1x15_P2.54mm_Horizontal.step
10.4 x 38.1 x 5.54 mm
