gowenrw/cowboys_vs_dinosaurs/eda/cowboys_vs_dinos/3d_models/C_0805_2012Metric.step

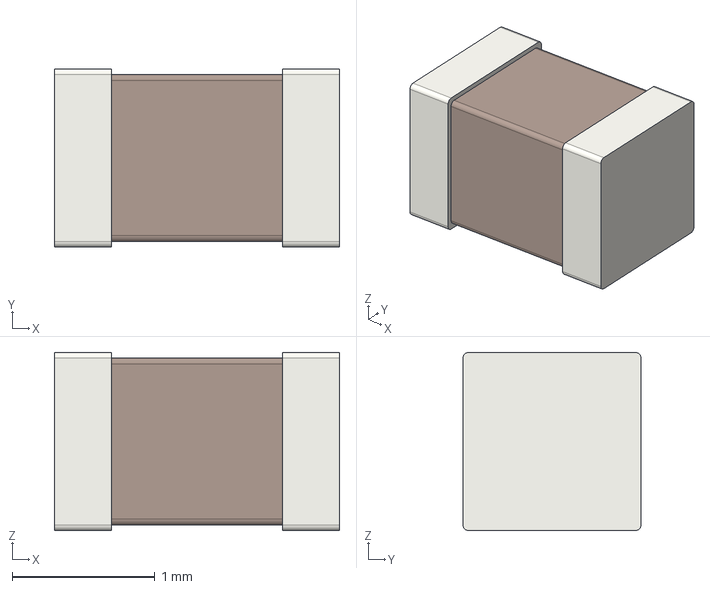
[picture p98: CAD file, 2024-03-11]
eda/cowboys_vs_dinos/3d_models/C_0805_2012Metric.step
2.00 x 1.25 x 1.25 mm
