gowenrw/cowboys_vs_dinosaurs/eda/cowboys_vs_dinos/3d_models/PinSocket_1x01_P2.54mm_Vertical.step

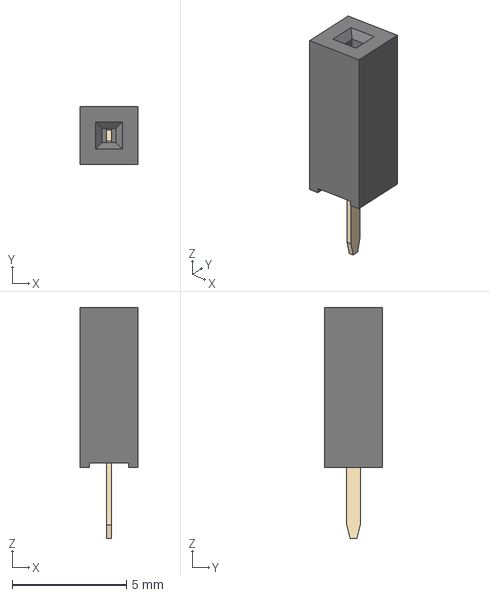
[picture p102: CAD file, 2024-03-11]
eda/cowboys_vs_dinos/3d_models/PinSocket_1x01_P2.54mm_Vertical.step
2.54 x 2.54 x 10.1 mm
