gowenrw/cowboys_vs_dinosaurs/eda/cowboys_vs_dinos/3d_models/LED_1206_3216Metric.step

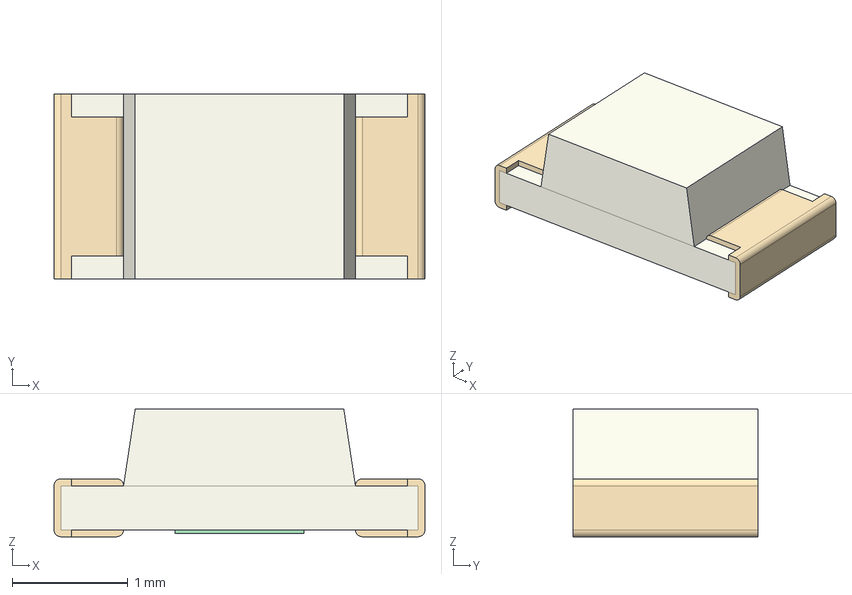
[picture p103: CAD file, 2024-03-11]
eda/cowboys_vs_dinos/3d_models/LED_1206_3216Metric.step
3.20 x 1.60 x 1.10 mm
