gowenrw/cowboys_vs_dinosaurs/eda/cowboys_vs_dinos/3d_models/PinHeader_1x20_P2.54mm_Horizontal.step

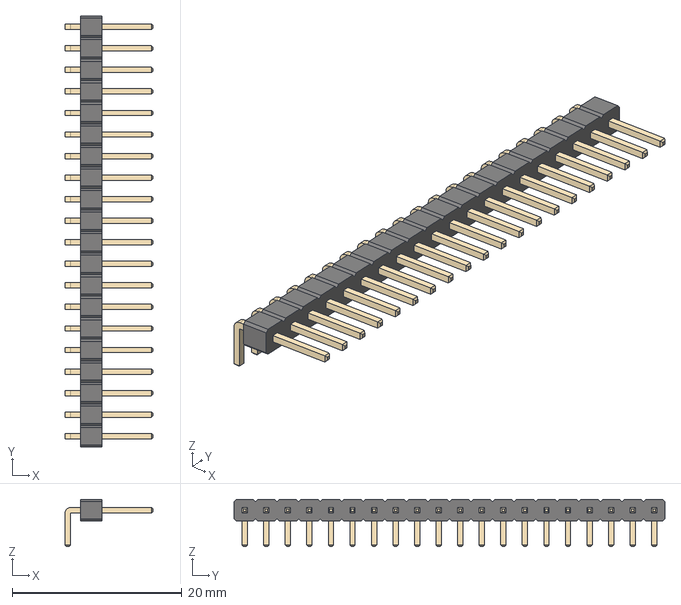
[picture p104: CAD file, 2024-03-11]
eda/cowboys_vs_dinos/3d_models/PinHeader_1x20_P2.54mm_Horizontal.step
10.4 x 50.8 x 5.54 mm
