gowenrw/cowboys_vs_dinosaurs/eda/cowboys_vs_dinos/3d_models/LED_D8.0mm.step

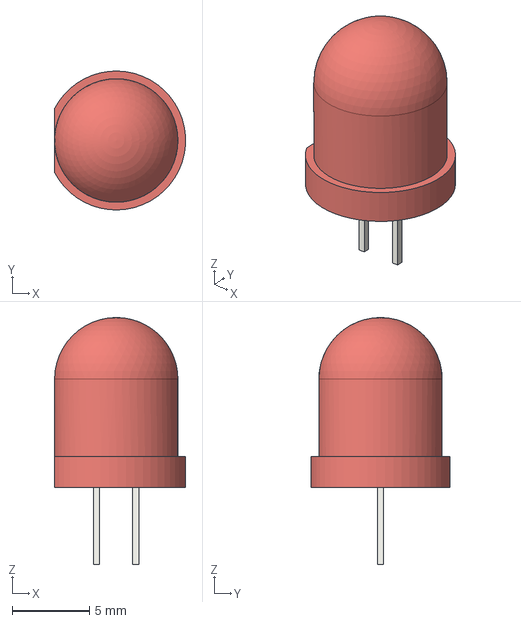
[picture p105: CAD file, 2024-03-11]
eda/cowboys_vs_dinos/3d_models/LED_D8.0mm.step
8.49 x 9.00 x 16.0 mm
