gowenrw/cowboys_vs_dinosaurs/eda/cowboys_vs_dinos/3d_models/Battery_Holder_3xAAA_Simple.step

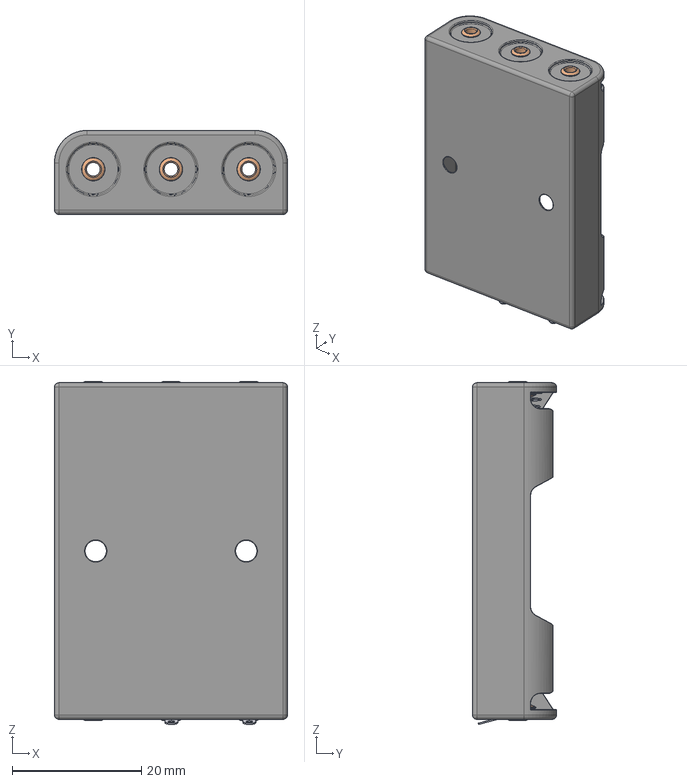
[picture p106: CAD file, 2024-03-11]
eda/cowboys_vs_dinos/3d_models/Battery_Holder_3xAAA_Simple.step
36.0 x 13.0 x 53.0 mm
