gowenrw/cowboys_vs_dinosaurs/eda/cowboys_vs_dinos/3d_models/GC9A01_1.28IN_240x240_v1.step

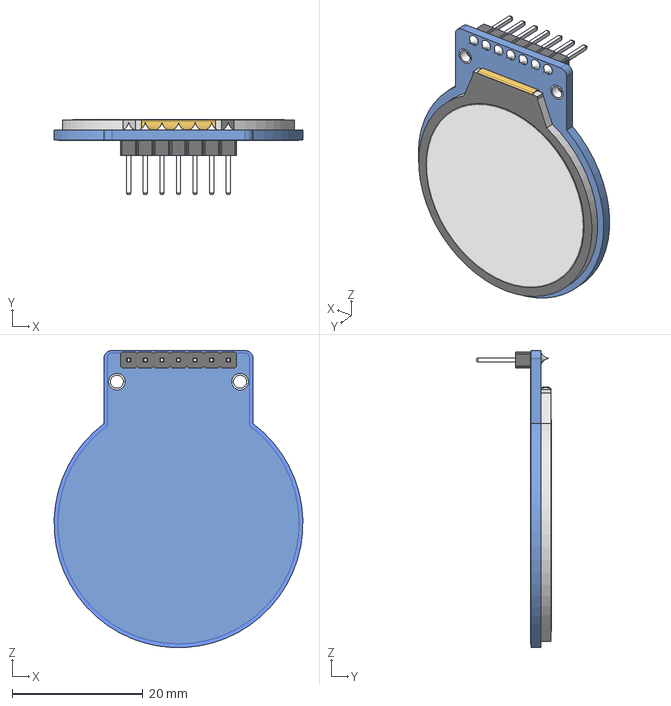
[picture p107: CAD file, 2024-03-11]
eda/cowboys_vs_dinos/3d_models/GC9A01_1.28IN_240x240_v1.step
38.1 x 11.5 x 45.5 mm
