gowenrw/cowboys_vs_dinosaurs/eda/cowboys_vs_dinos/3d_models/PinHeader_1x10_P2.54mm_Vertical.step

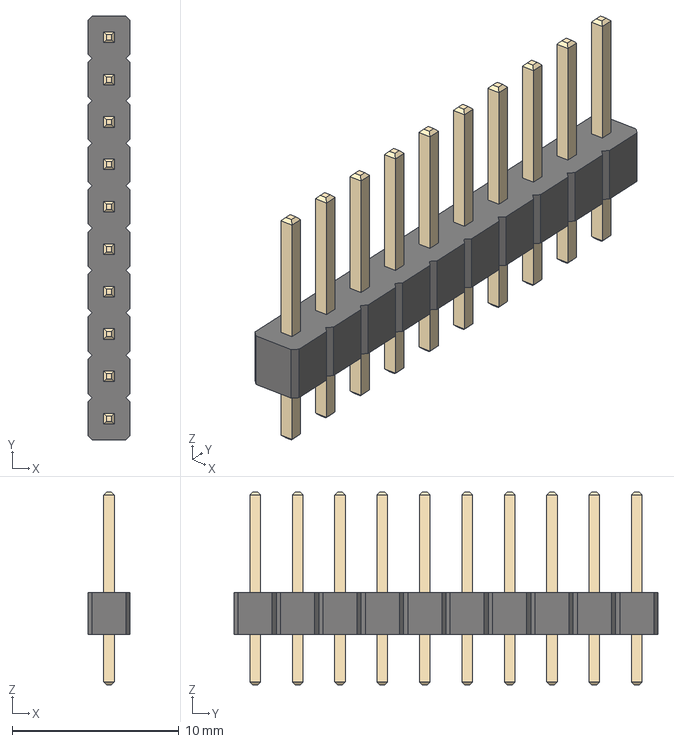
[picture p108: CAD file, 2024-03-11]
eda/cowboys_vs_dinos/3d_models/PinHeader_1x10_P2.54mm_Vertical.step
2.54 x 25.4 x 11.5 mm
