gowenrw/cowboys_vs_dinosaurs/eda/cowboys_vs_dinos/3d_models/SW_SS12D00G-Mini-SPDT-Slide-Switch-3pin-1P2T-2-Position-Toggle-Switch-3D.step

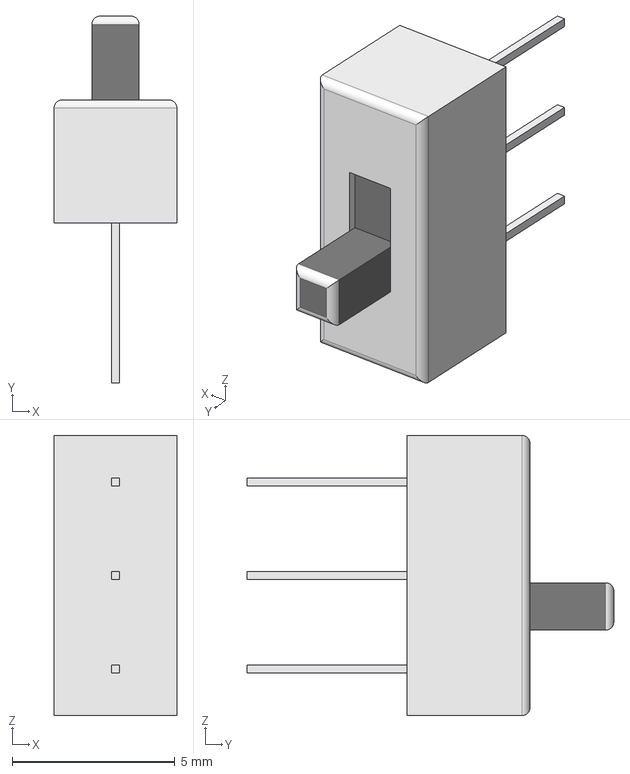
[picture p116: CAD file, 2024-03-11]
eda/cowboys_vs_dinos/3d_models/SW_SS12D00G-Mini-SPDT-Slide-Switch-3pin-1P2T-2-Position-Toggle-Switch-3D.step
3.77 x 11.2 x 8.59 mm
