gowenrw/cowboys_vs_dinosaurs/eda/cowboys_vs_dinos/3d_models/BatteryHolder_2466_1xAAA.step

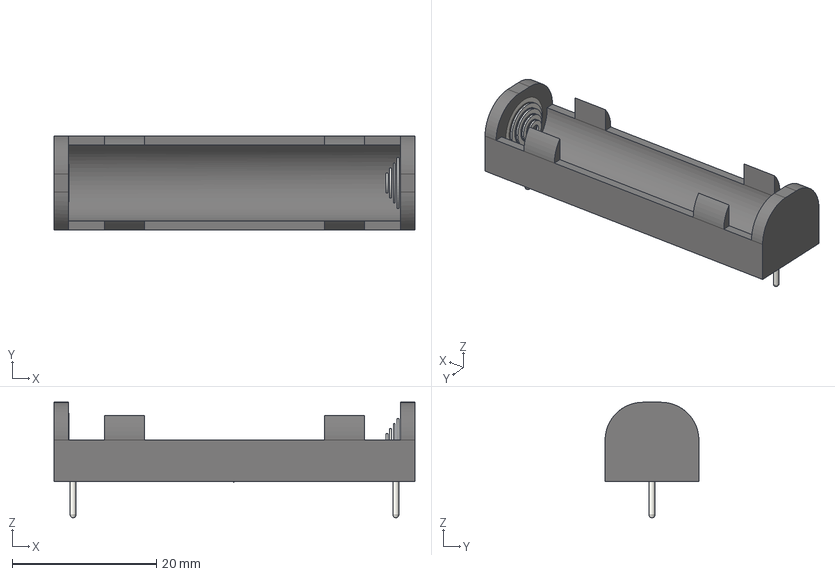
[picture p118: CAD file, 2024-03-11]
eda/cowboys_vs_dinos/3d_models/BatteryHolder_2466_1xAAA.step
50.0 x 13.0 x 16.0 mm
