gowenrw/cowboys_vs_dinosaurs/eda/cowboys_vs_dinos/3d_models/C_Rect_L4.6mm_W2.0mm_P2.50mm_MKS02_FKP02.step

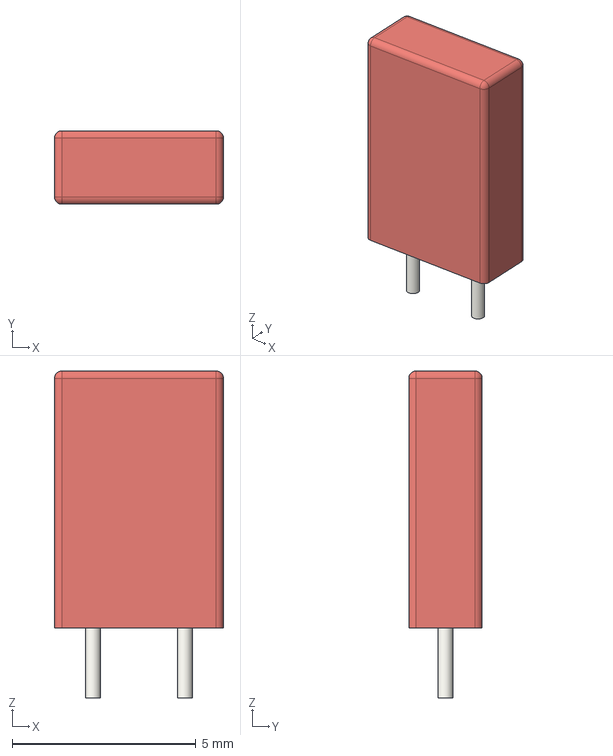
[picture p120: CAD file, 2024-03-11]
eda/cowboys_vs_dinos/3d_models/C_Rect_L4.6mm_W2.0mm_P2.50mm_MKS02_FKP02.step
4.60 x 2.00 x 8.90 mm
