gowenrw/cowboys_vs_dinosaurs/eda/cowboys_vs_dinos/3d_models/PinSocket_1x06_P2.54mm_Vertical.step

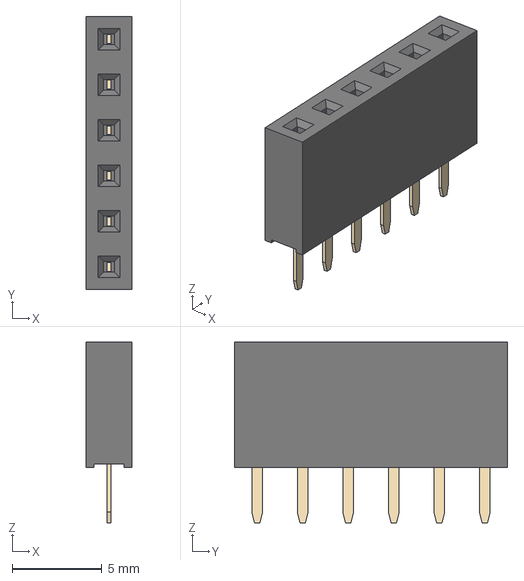
[picture p121: CAD file, 2024-03-11]
eda/cowboys_vs_dinos/3d_models/PinSocket_1x06_P2.54mm_Vertical.step
2.54 x 15.2 x 10.1 mm
