gowenrw/cowboys_vs_dinosaurs/eda/cowboys_vs_dinos/3d_models/PinHeader_1x07_P2.54mm_Vertical.step

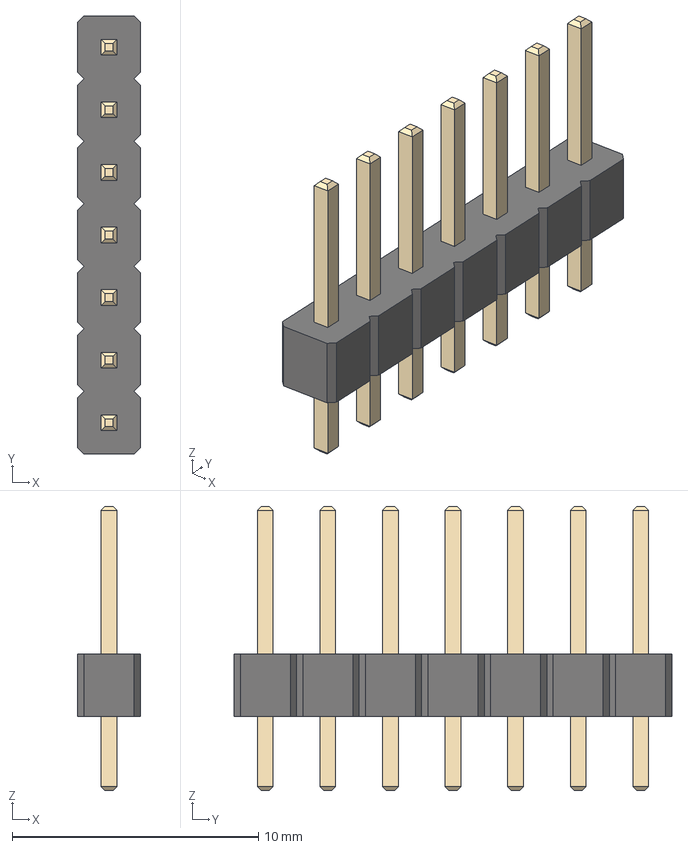
[picture p122: CAD file, 2024-03-11]
eda/cowboys_vs_dinos/3d_models/PinHeader_1x07_P2.54mm_Vertical.step
2.54 x 17.8 x 11.5 mm
