gowenrw/cowboys_vs_dinosaurs/eda/cowboys_vs_dinos/3d_models/C_0603_1608Metric.step

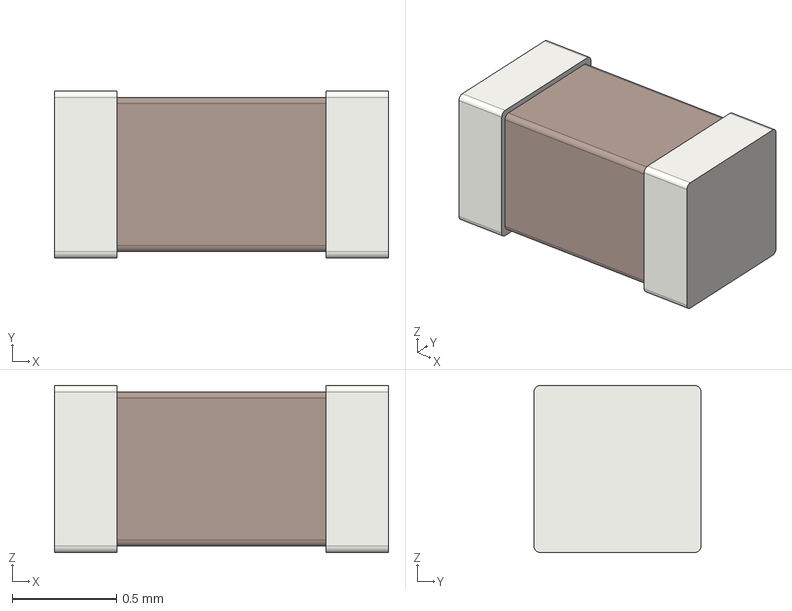
[picture p123: CAD file, 2024-03-11]
eda/cowboys_vs_dinos/3d_models/C_0603_1608Metric.step
1.60 x 0.8 x 0.8 mm
