gowenrw/cowboys_vs_dinosaurs/eda/cowboys_vs_dinos/3d_models/LED_D5.0mm.step

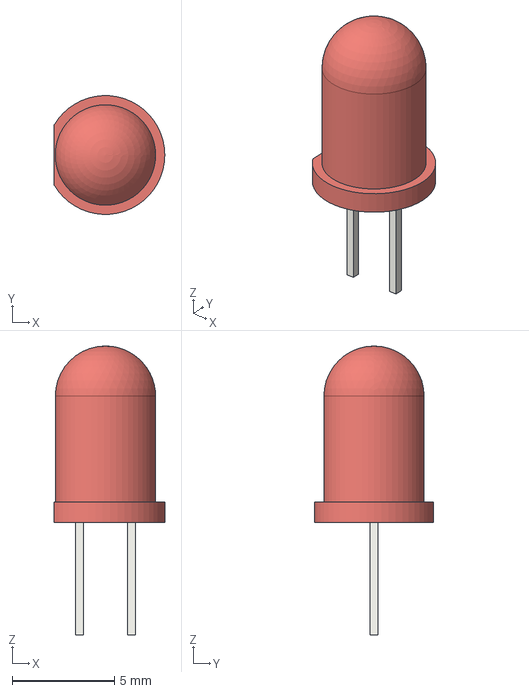
[picture p126: CAD file, 2024-03-11]
eda/cowboys_vs_dinos/3d_models/LED_D5.0mm.step
5.40 x 5.79 x 14.1 mm
