gowenrw/cowboys_vs_dinosaurs/eda/cowboys_vs_dinos/3d_models/TS2306A.step

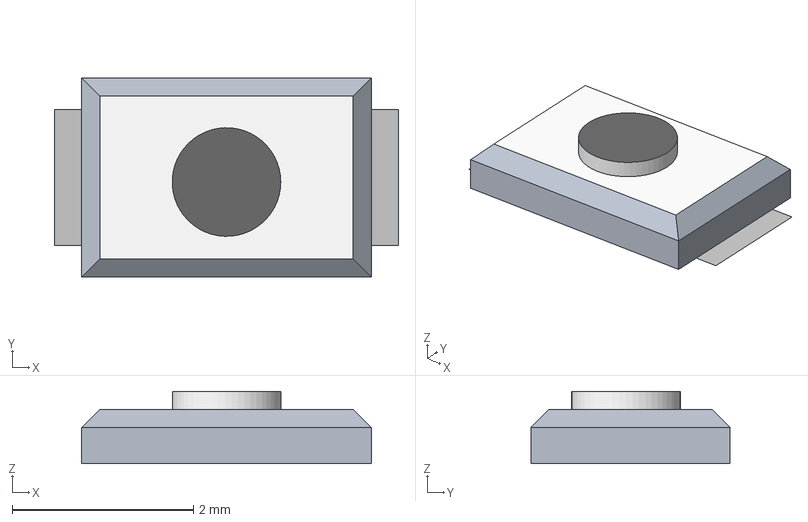
[picture p127: CAD file, 2024-03-11]
eda/cowboys_vs_dinos/3d_models/TS2306A.step
3.80 x 2.20 x 0.8 mm
Plane
