gowenrw/cowboys_vs_dinosaurs/eda/cowboys_vs_dinos/3d_models/CP_Radial_D5.0mm_P2.00mm.step

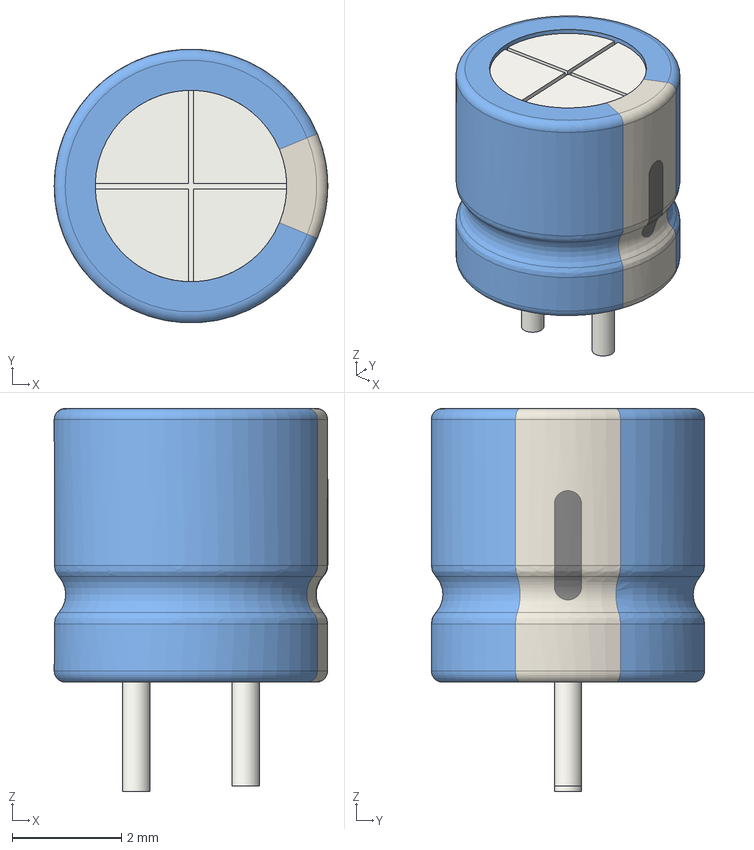
[picture p129: CAD file, 2024-03-11]
eda/cowboys_vs_dinos/3d_models/CP_Radial_D5.0mm_P2.00mm.step
5.00 x 5.00 x 7.00 mm
