gowenrw/cowboys_vs_dinosaurs/eda/cowboys_vs_dinos/3d_models/LED_D3.0mm-3.step

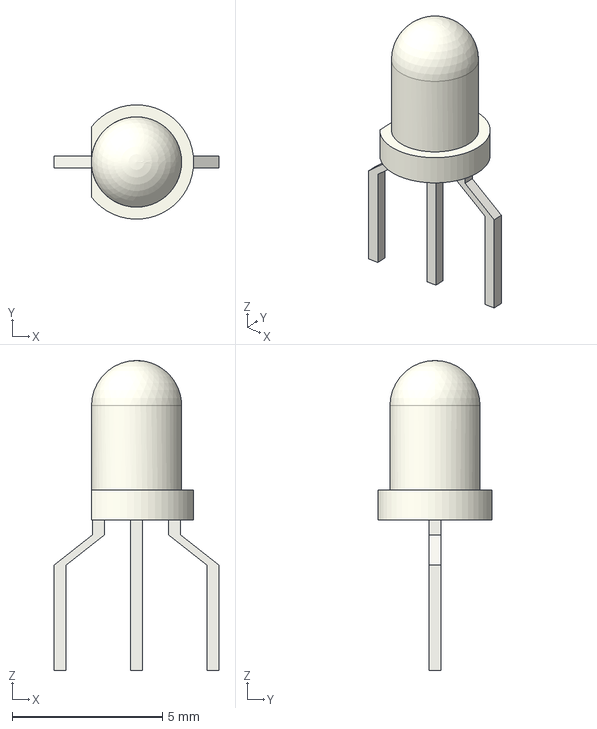
[picture p130: CAD file, 2024-03-11]
eda/cowboys_vs_dinos/3d_models/LED_D3.0mm-3.step
5.48 x 3.80 x 10.3 mm
