gowenrw/cowboys_vs_dinosaurs/eda/cowboys_vs_dinos/3d_models/C_Disc_D3.0mm_W2.0mm_P2.50mm.step

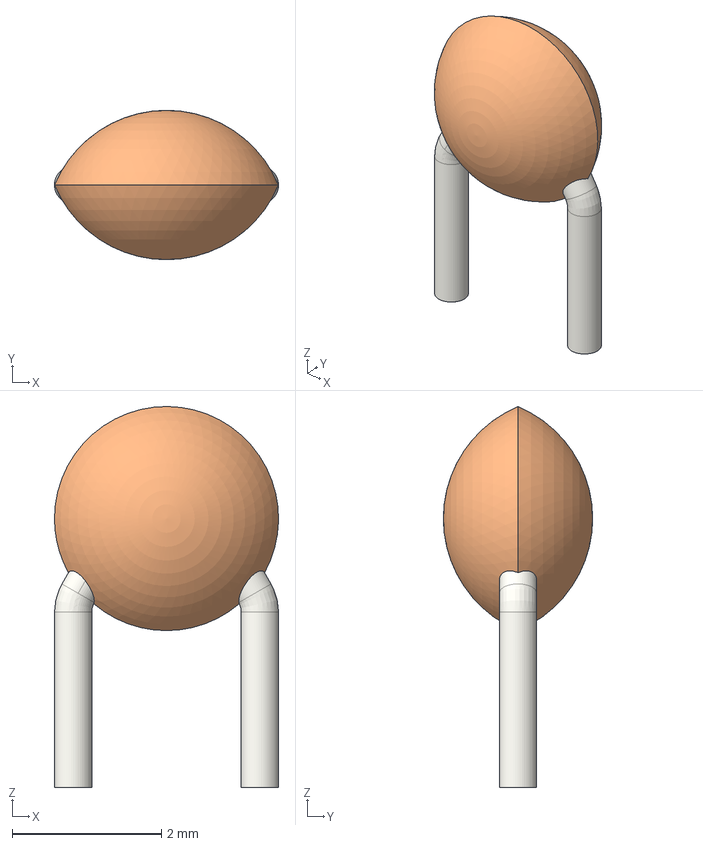
[picture p135: CAD file, 2024-03-11]
eda/cowboys_vs_dinos/3d_models/C_Disc_D3.0mm_W2.0mm_P2.50mm.step
3.00 x 2.00 x 5.10 mm
