gowenrw/cowboys_vs_dinosaurs/eda/cowboys_vs_dinos/3d_models/PinHeader_1x20_P2.54mm_Vertical.step

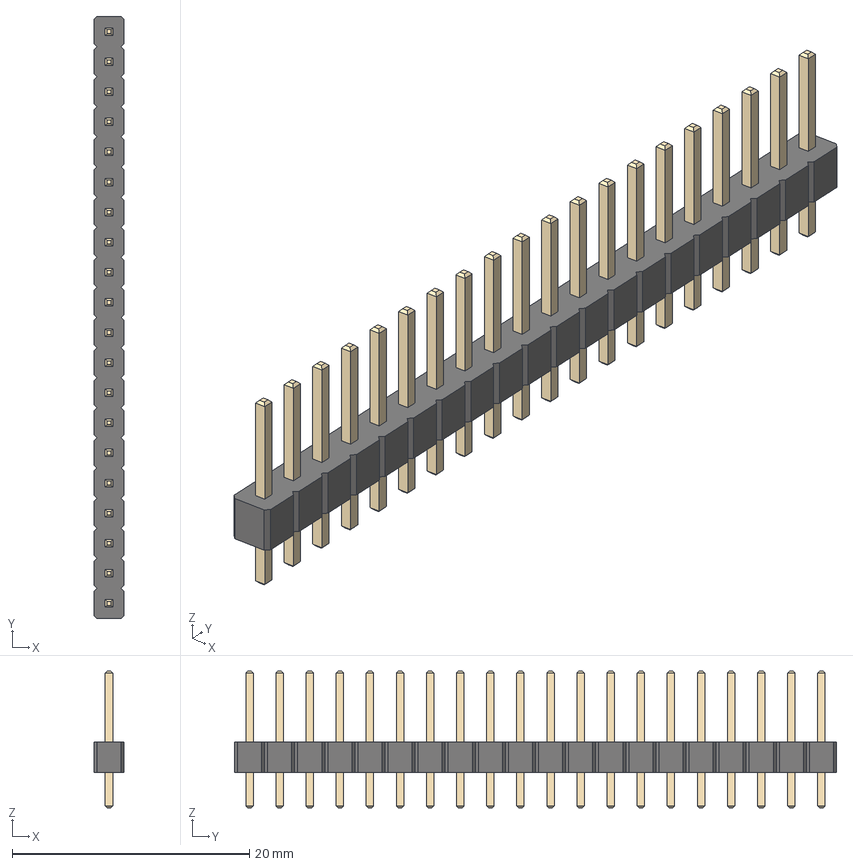
[picture p137: CAD file, 2024-03-11]
eda/cowboys_vs_dinos/3d_models/PinHeader_1x20_P2.54mm_Vertical.step
2.54 x 50.8 x 11.5 mm
