gowenrw/cowboys_vs_dinosaurs/eda/cowboys_vs_dinos/3d_models/R_Axial_DIN0204_L3.6mm_D1.6mm_P5.08mm_Horizontal.step

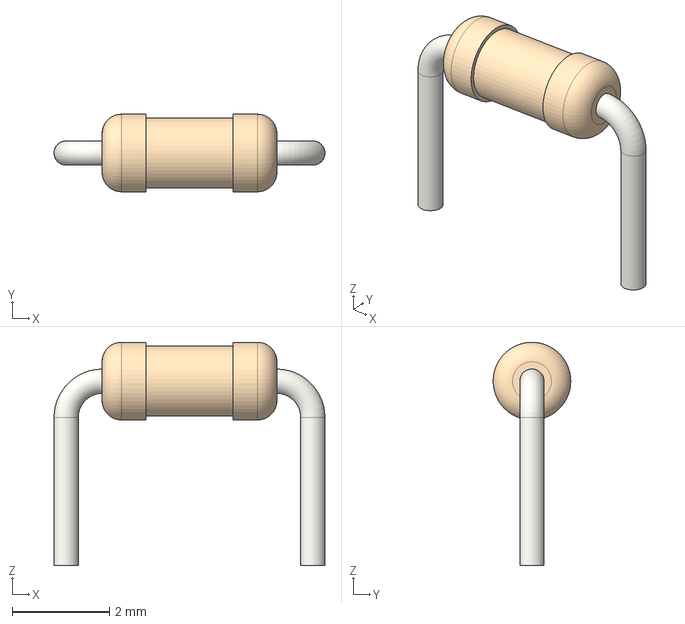
[picture p138: CAD file, 2024-03-11]
eda/cowboys_vs_dinos/3d_models/R_Axial_DIN0204_L3.6mm_D1.6mm_P5.08mm_Horizontal.step
5.58 x 1.60 x 4.60 mm
