gowenrw/cowboys_vs_dinosaurs/eda/cowboys_vs_dinos/3d_models/R_0805_2012Metric.step

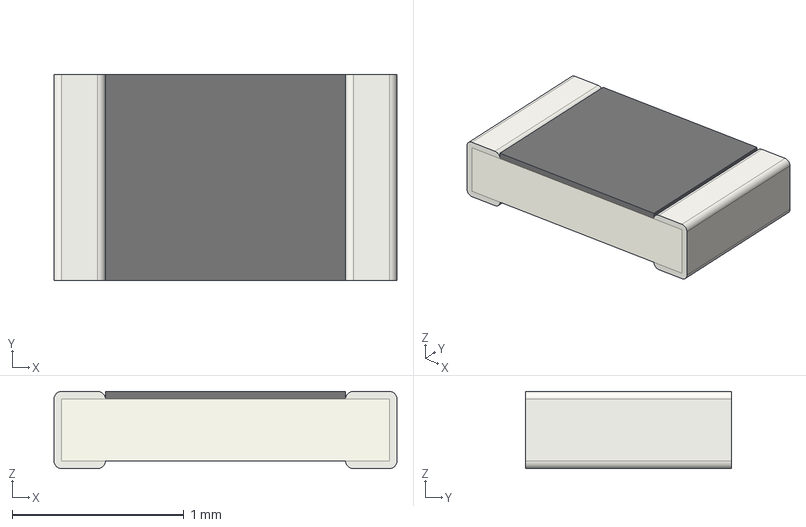
[picture p139: CAD file, 2024-03-11]
eda/cowboys_vs_dinos/3d_models/R_0805_2012Metric.step
2.00 x 1.20 x 0.45 mm
