gowenrw/cowboys_vs_dinosaurs/eda/cowboys_vs_dinos/3d_models/RJ45_Amphenol_RJHSE-5080-56544.STEP

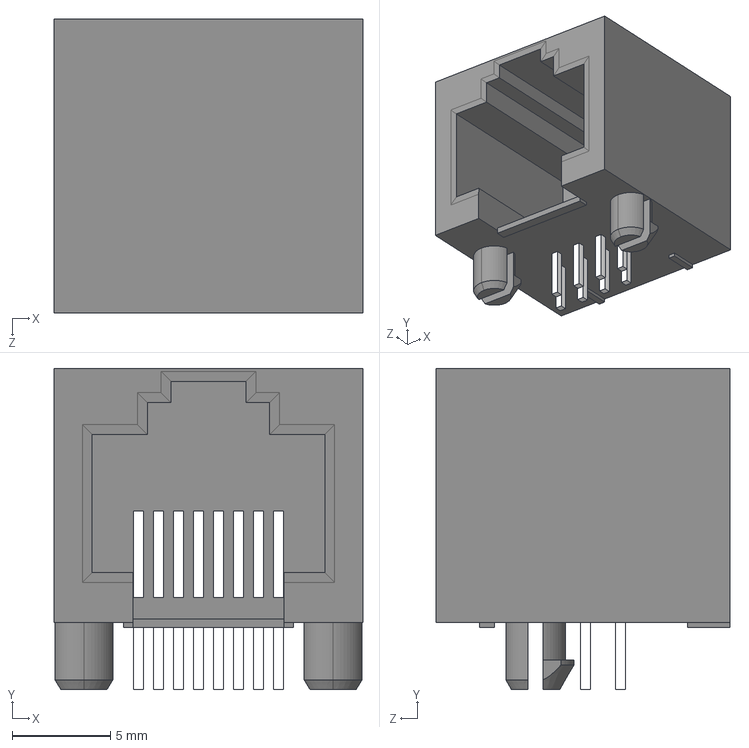
[picture p141: CAD file, 2024-03-11]
eda/cowboys_vs_dinos/3d_models/RJ45_Amphenol_RJHSE-5080-56544.STEP
15.7 x 16.4 x 15.0 mm
