gowenrw/cowboys_vs_dinosaurs/eda/cowboys_vs_dinos/3d_models/BatteryHolder_2468_2xAAA.step

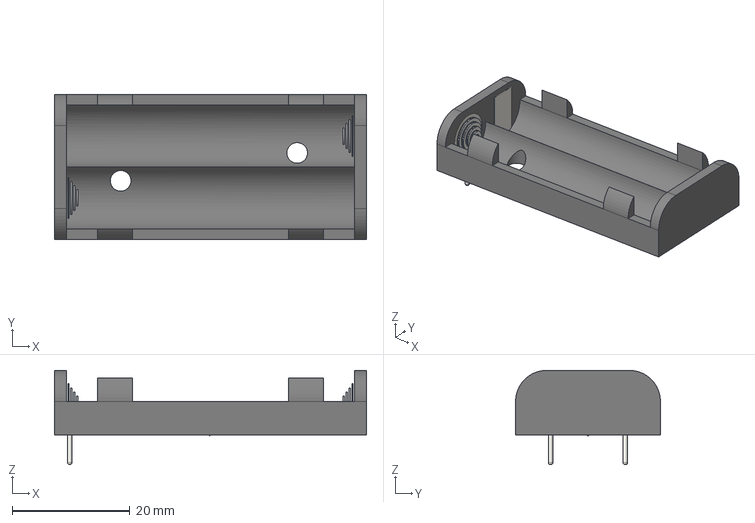
[picture p142: CAD file, 2024-03-11]
eda/cowboys_vs_dinos/3d_models/BatteryHolder_2468_2xAAA.step
53.0 x 24.6 x 16.0 mm
