gowenrw/cowboys_vs_dinosaurs/eda/cowboys_vs_dinos/3d_models/C_1206_3216Metric.step

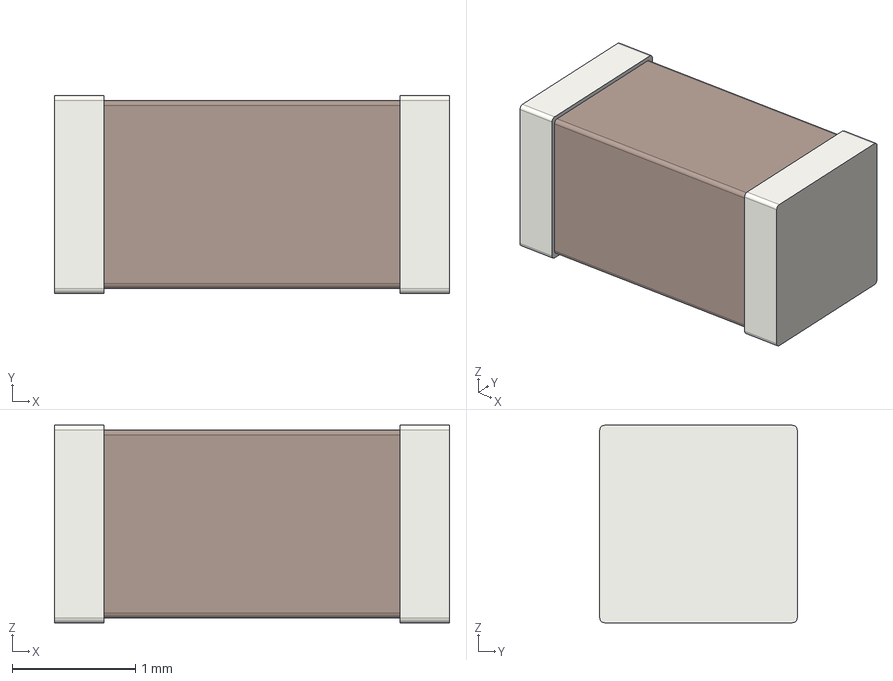
[picture p143: CAD file, 2024-03-11]
eda/cowboys_vs_dinos/3d_models/C_1206_3216Metric.step
3.20 x 1.60 x 1.60 mm
