gowenrw/cowboys_vs_dinosaurs/eda/cowboys_vs_dinos/3d_models/PinSocket_1x05_P2.54mm_Horizontal.step

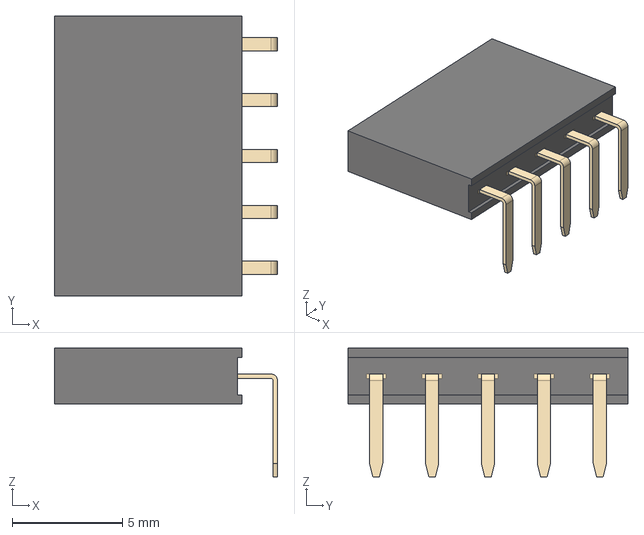
[picture p147: CAD file, 2024-03-11]
eda/cowboys_vs_dinos/3d_models/PinSocket_1x05_P2.54mm_Horizontal.step
10.1 x 12.7 x 5.84 mm
