gowenrw/cowboys_vs_dinosaurs/eda/cowboys_vs_dinos/3d_models/SOT-23.step

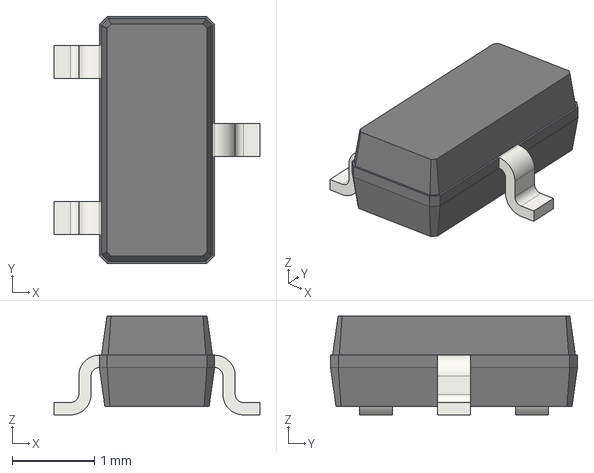
[picture p148: CAD file, 2024-03-11]
eda/cowboys_vs_dinos/3d_models/SOT-23.step
2.50 x 3.00 x 1.20 mm
