gowenrw/cowboys_vs_dinosaurs/eda/cowboys_vs_dinos/3d_models/SW_PUSH_6mm.step

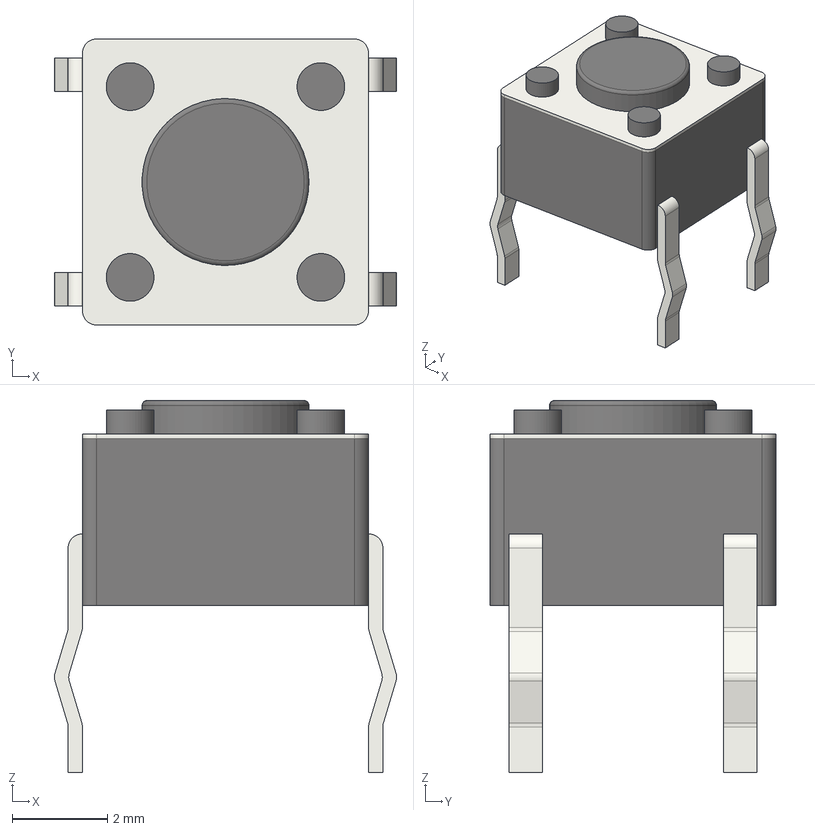
[picture p153: CAD file, 2024-03-11]
eda/cowboys_vs_dinos/3d_models/SW_PUSH_6mm.step
7.17 x 6.00 x 7.80 mm
