gowenrw/cowboys_vs_dinosaurs/eda/cowboys_vs_dinos/3d_models/PinSocket_1x09_P2.54mm_Horizontal.step

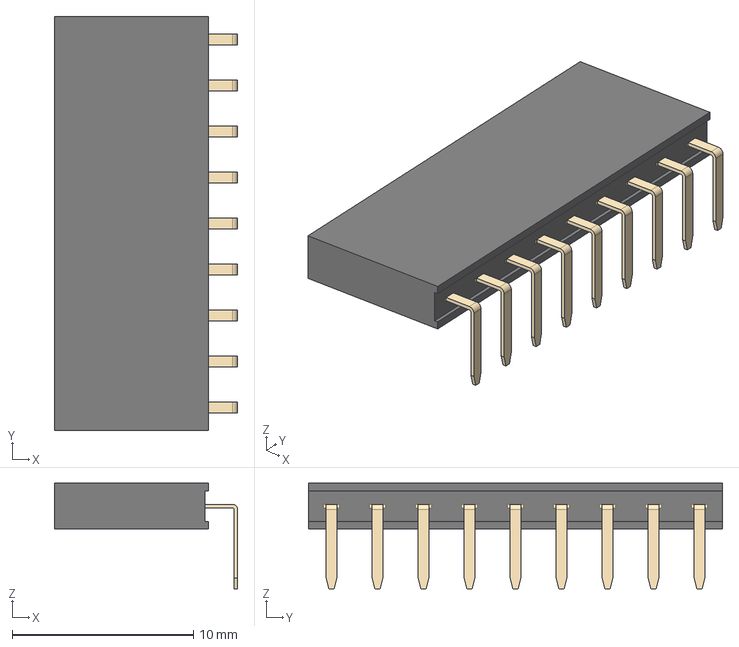
[picture p154: CAD file, 2024-03-11]
eda/cowboys_vs_dinos/3d_models/PinSocket_1x09_P2.54mm_Horizontal.step
10.1 x 22.9 x 5.84 mm
