gowenrw/cowboys_vs_dinosaurs/eda/cowboys_vs_dinos/3d_models/R_Axial_DIN0207_L6.3mm_D2.5mm_P7.62mm_Horizontal.step

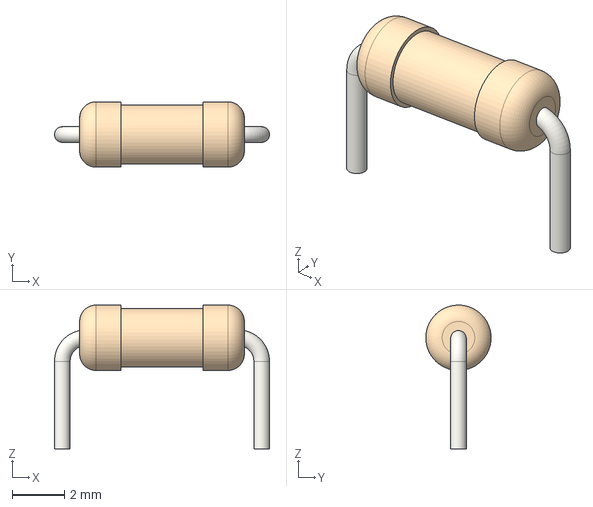
[picture p157: CAD file, 2024-03-11]
eda/cowboys_vs_dinos/3d_models/R_Axial_DIN0207_L6.3mm_D2.5mm_P7.62mm_Horizontal.step
8.22 x 2.50 x 5.50 mm
