gowenrw/cowboys_vs_dinosaurs/eda/cowboys_vs_dinos/3d_models/RJ45_Amphenol_RJHSE538X.step

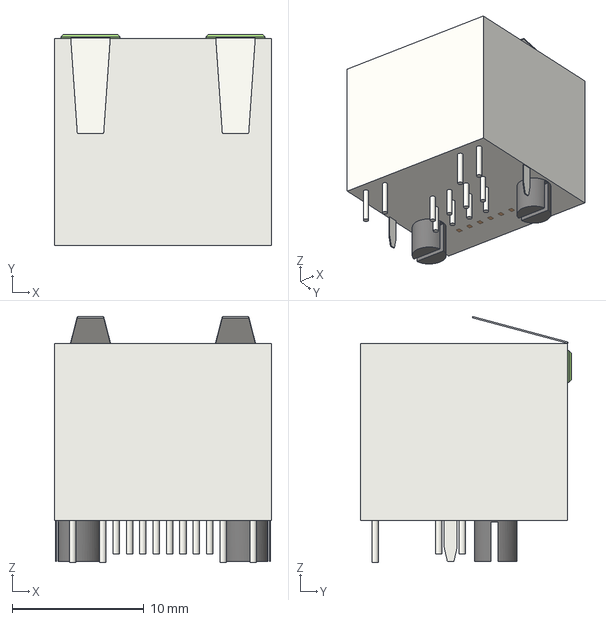
[picture p159: CAD file, 2024-03-11]
eda/cowboys_vs_dinos/3d_models/RJ45_Amphenol_RJHSE538X.step
16.5 x 16.1 x 18.7 mm
