gowenrw/cowboys_vs_dinosaurs/docs/AssemblyPicture10.jpg

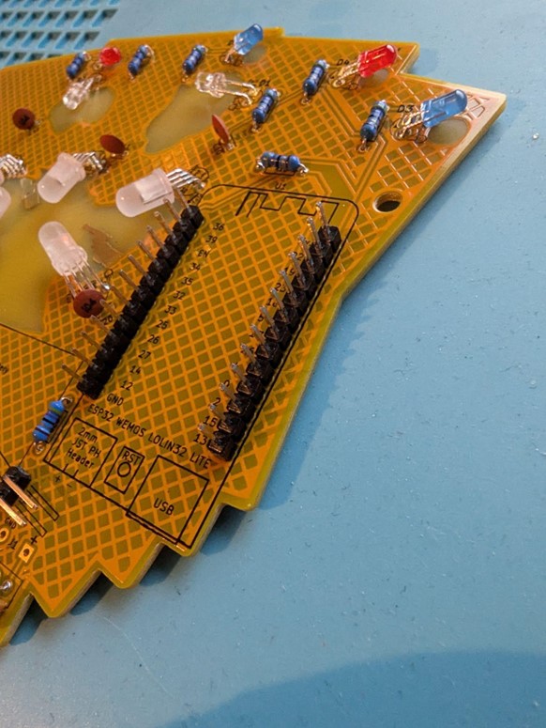
docs/AssemblyPicture10.jpg
