gowenrw/cowboys_vs_dinosaurs/docs/AssemblyPicture17.jpg

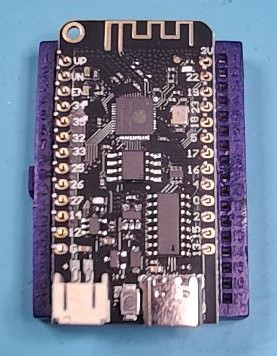
docs/AssemblyPicture17.jpg
