gowenrw/cowboys_vs_dinosaurs/docs/blink_poc_02_test_circuit.jpg

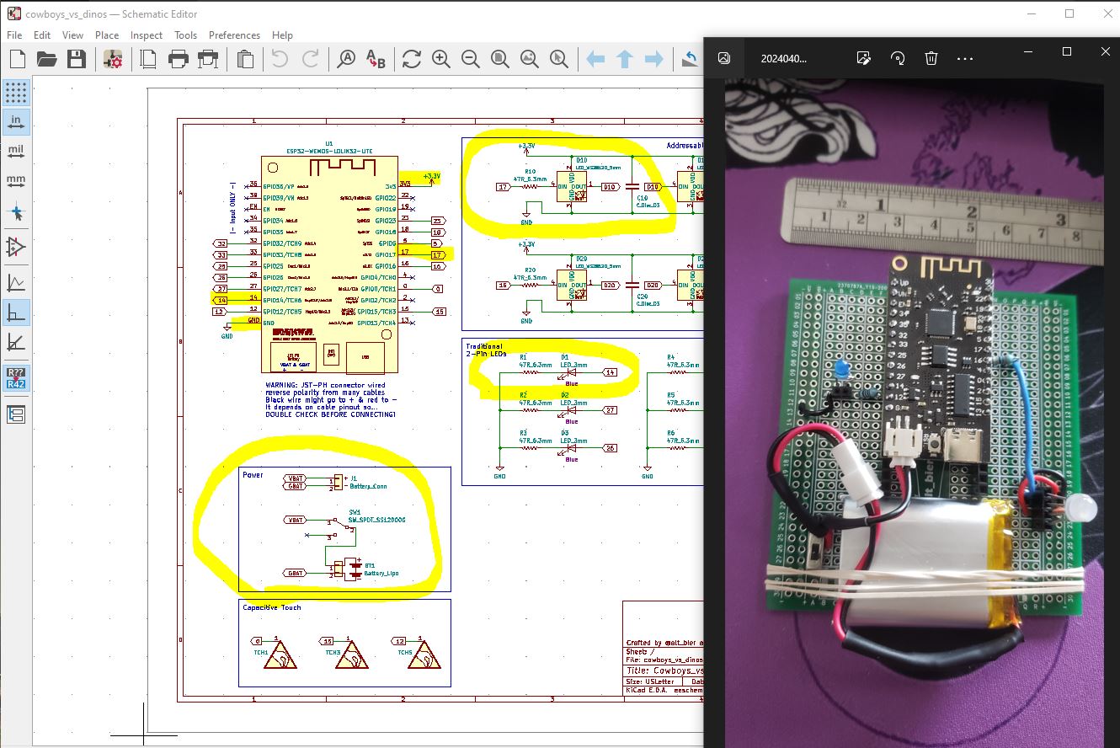
docs/blink_poc_02_test_circuit.jpg
