gowenrw/cowboys_vs_dinosaurs/docs/blink_poc_02_test_circuit_schem.jpg

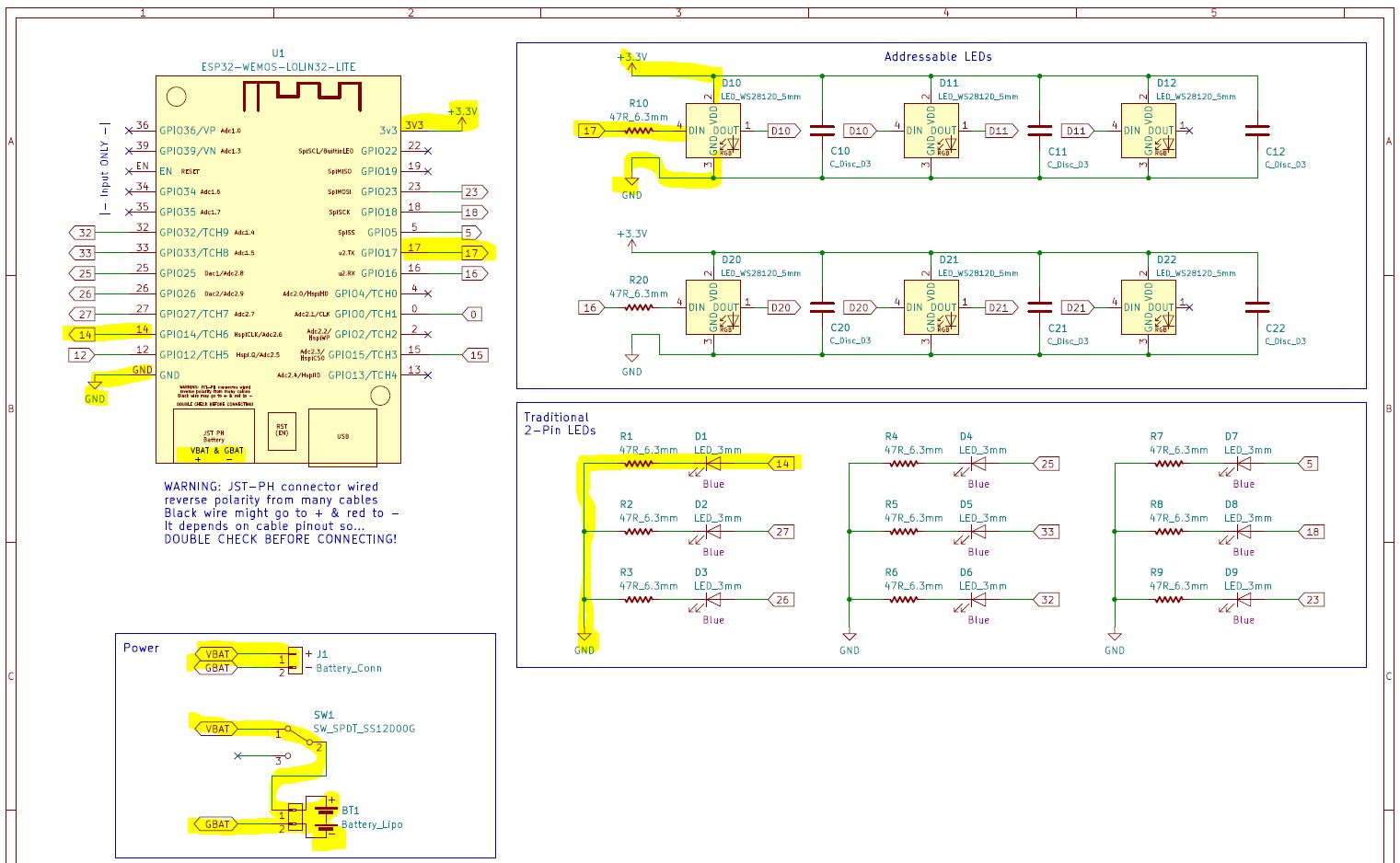
docs/blink_poc_02_test_circuit_schem.jpg
