gowenrw/cowboys_vs_dinosaurs/eda/cowboys_vs_dinos/cowboys_vs_dinos.kicad_sch

## KiCad design eda/cowboys_vs_dinos/cowboys_vs_dinos.kicad_sch (2024-05-06, an earlier design)

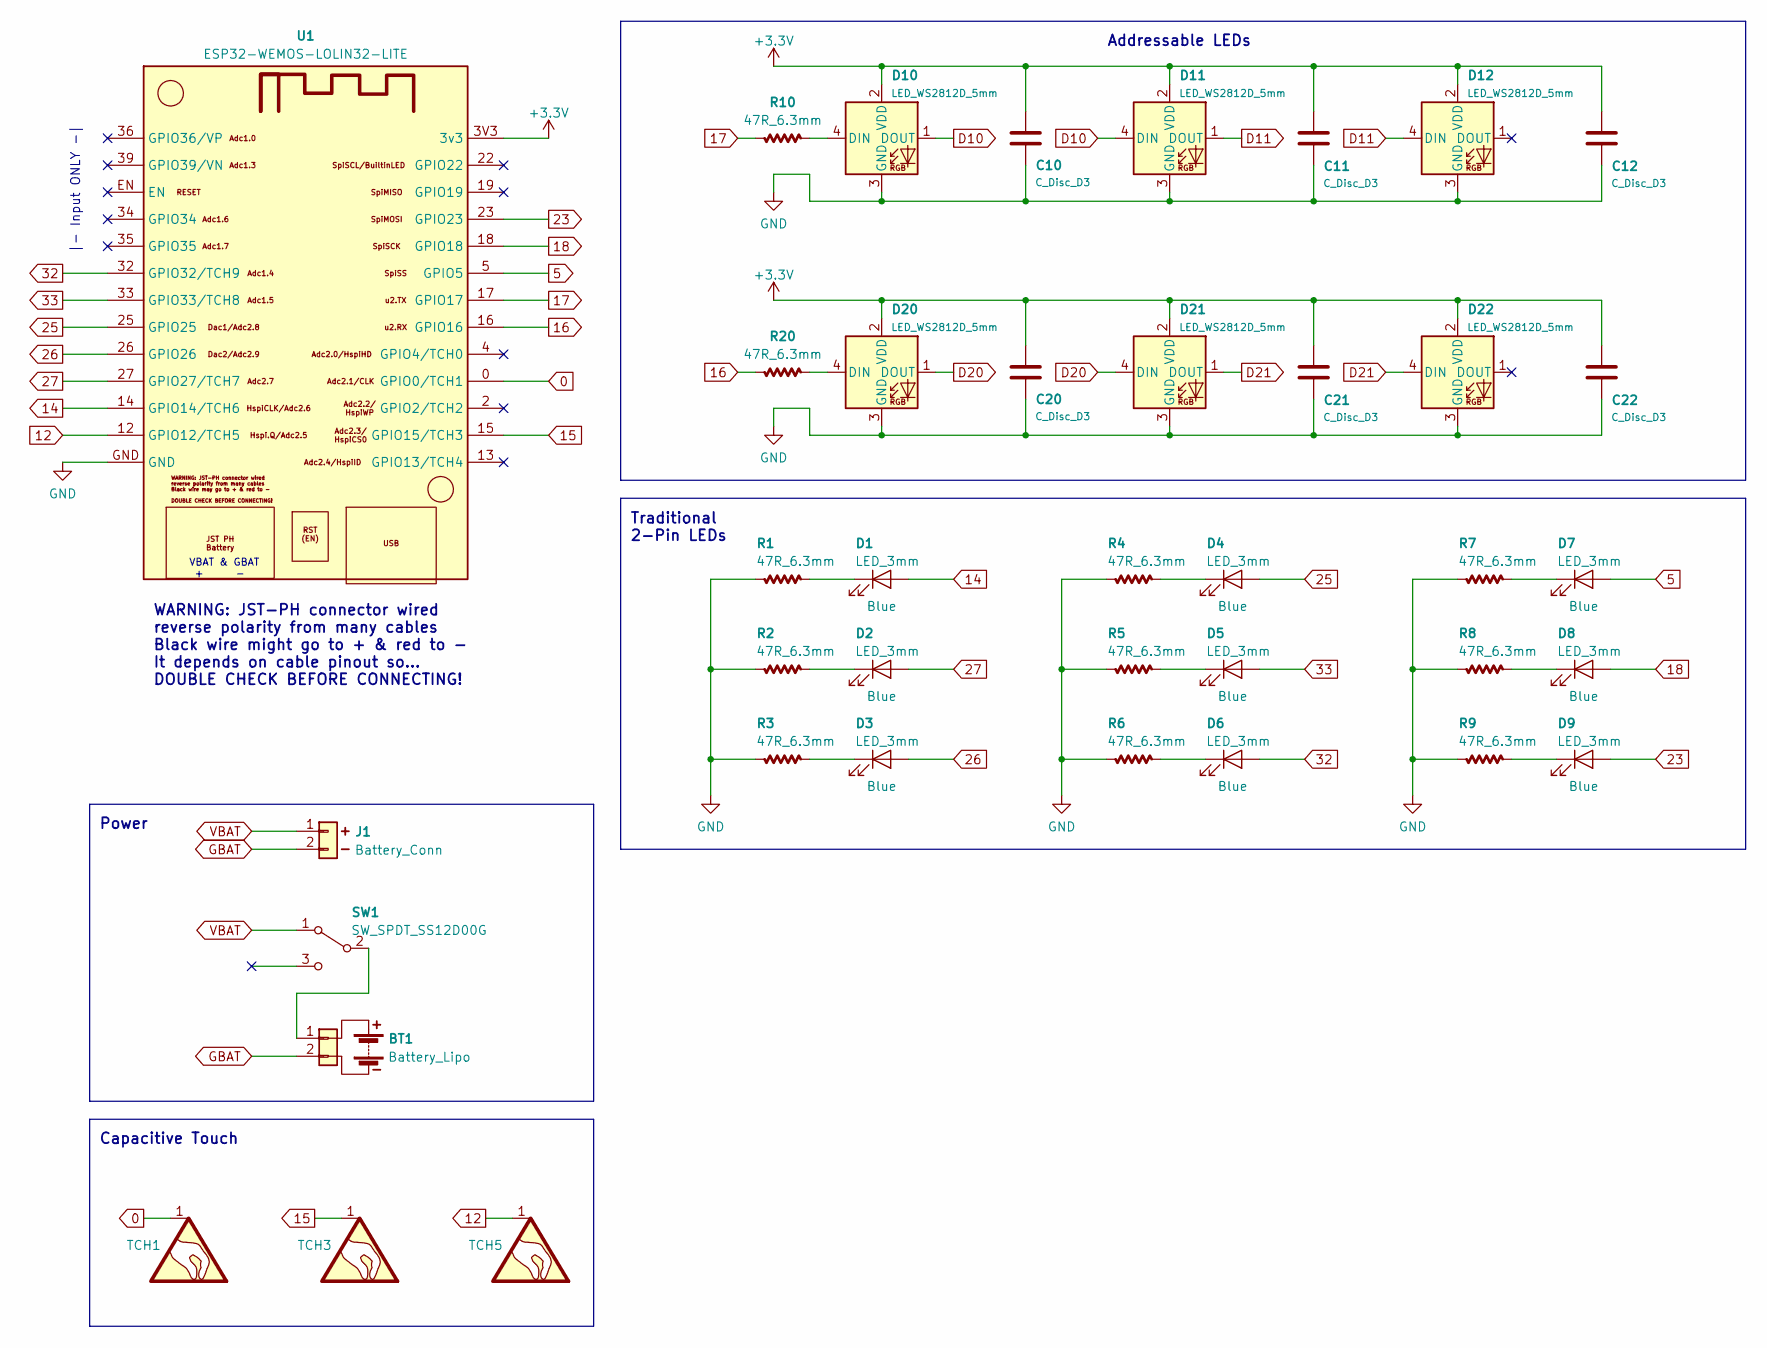
[picture p215: schematic cowboys_vs_dinos.kicad_sch]

Parts:
BT1: Battery_Lipo; Battery_Connector_back
C10, C11, C12, C20, C21, C22: C_Disc_D3; C_Disc_D3_back
D1, D2, D3, D4, D5, D6, D7, D8, D9: LED_3mm; LED_D3.0mm-2-std_back
D10, D11, D12, D20, D21, D22: LED_WS2812D_5mm; LED_D5.0mm-4_WS2812D_2024_back
J1: Battery_Conn; Battery_Connector_back
R1, R2, R3, R4, R5, R6, R7, R8, R9, R10, R20: 47R_6.3mm; R_Axial_DIN0207_L6.3_D2.5_P7.62_Horiz_back
SW1: SW_SPDT_SS12D00G; SW_SPDT_Slide_SS12D00G-1P2T_3pin_back
TCH1, TCH3, TCH5: SYM_Touch_lg
U1: ESP32-WEMOS-LOLIN32-LITE; ESP32_WEMOS_LOLIN32_LITE_back

Connections:
0: TCH1.1, U1.0 (GPIO0/TCH1)
5: D7.2 (A), U1.5 (GPIO5)
12: TCH5.1, U1.12 (GPIO12/TCH5)
14: D1.2 (A), U1.14 (GPIO14/TCH6)
15: TCH3.1, U1.15 (GPIO15/TCH3)
16: R20.2, U1.16 (GPIO16)
17: R10.2, U1.17 (GPIO17)
18: D8.2 (A), U1.18 (GPIO18)
23: D9.2 (A), U1.23 (GPIO23)
25: D4.2 (A), U1.25 (GPIO25)
26: D3.2 (A), U1.26 (GPIO26)
27: D2.2 (A), U1.27 (GPIO27/TCH7)
32: D6.2 (A), U1.32 (GPIO32/TCH9)
33: D5.2 (A), U1.33 (GPIO33/TCH8)
+3.3V: C10.1, C11.1, C12.1, C20.1, C21.1, C22.1, D10.2 (VDD), D11.2 (VDD), D12.2 (VDD), D20.2 (VDD), D21.2 (VDD), D22.2 (VDD), U1.3V3 (3v3)
D10: D10.1 (DOUT), D11.4 (DIN)
D11: D11.1 (DOUT), D12.4 (DIN)
D20: D20.1 (DOUT), D21.4 (DIN)
D21: D21.1 (DOUT), D22.4 (DIN)
GBAT: BT1.2, J1.2
GND: C10.2, C11.2, C12.2, C20.2, C21.2, C22.2, D10.3 (GND), D11.3 (GND), D12.3 (GND), D20.3 (GND), D21.3 (GND), D22.3 (GND), R1.2, R2.2, R3.2, R4.2, R5.2, R6.2, R7.2, R8.2, R9.2, U1.GND
unnamed: BT1.1, SW1.2 (B)
unnamed: D1.1 (K), R1.1
unnamed: D2.1 (K), R2.1
unnamed: D3.1 (K), R3.1
unnamed: D4.1 (K), R4.1
unnamed: D5.1 (K), R5.1
unnamed: D6.1 (K), R6.1
unnamed: D7.1 (K), R7.1
unnamed: D8.1 (K), R8.1
unnamed: D9.1 (K), R9.1
unnamed: D10.4 (DIN), R10.1
unnamed: D20.4 (DIN), R20.1
VBAT: J1.1, SW1.1 (A)

Notes on the sheet:
Addressable LEDs
|- Input ONLY -|
VBAT & GBAT + -
Capacitive Touch
WARNING: JST-PH connector wired reverse polarity from many cables Black wire might go to + & red to - It depends on cable pinout so... DOUBLE CHECK BEFORE CONNECTING!
Traditional 2-Pin LEDs
Power
